3d-paws/3D-PAWS-Print-Files/Rain Gauge Calibration/calibration parts.3mf

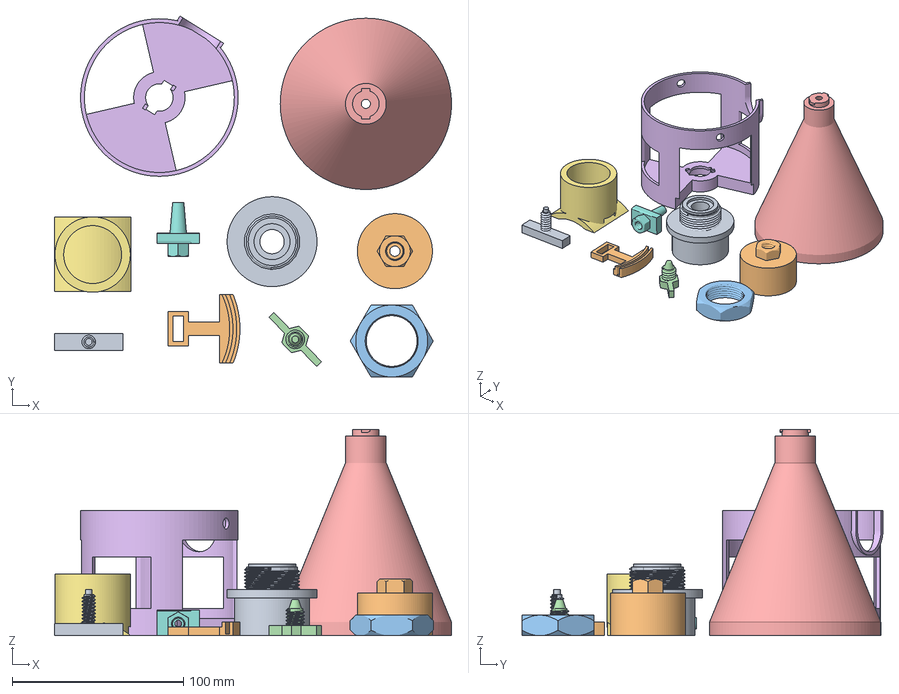
[picture p15: CAD file, 2026-02-17]
Rain Gauge Calibration/calibration parts.3mf
231.8 x 210.8 x 120.5 mm
CF valve top.stl
CF valve bottom for dip bolt2.stl
box to pipe adaptor nut2.stl
drip bolt.stl
funnel small.stl
inspection cover.stl
universal clamp for 1 in pipe.stl
pumped drip controller2.stl
pumped drip controller piston.stl
pumped drip controller mount.stl
