3d-paws/3D-PAWS-Print-Files/Rain Gauge/Funnel/vertical screen.stl

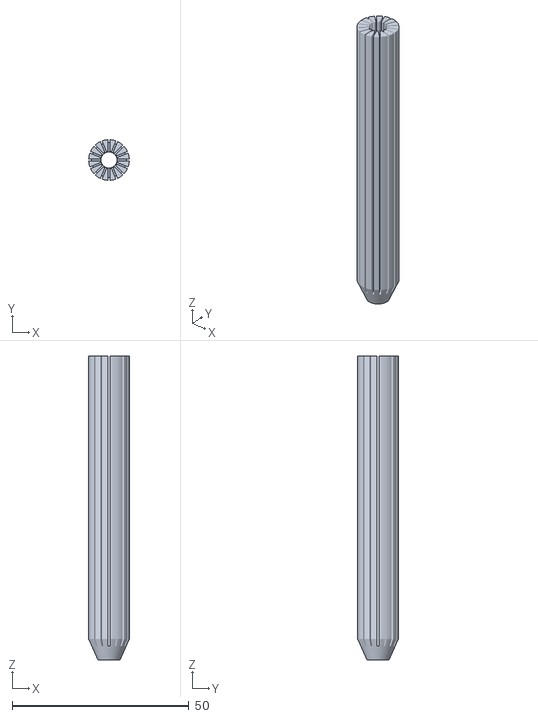
[picture p16: CAD file, 2025-01-10]
Rain Gauge/Funnel/vertical screen.stl
11.5 x 11.5 x 85.9
