3d-paws/3D-PAWS-Print-Files/Snow Gauge/Snow_Gauge.3mf

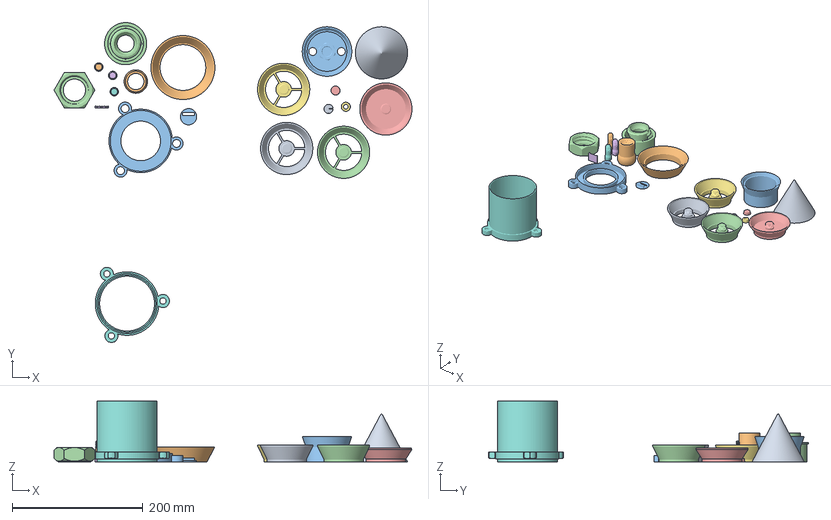
[picture p17: CAD file, 2026-01-30]
Snow Gauge/Snow_Gauge.3mf
548.4 x 490.0 x 93.0 mm
snow cone cover.stl
swivel.stl
Snow gauge rad shield base.stl
swivel lock nut.stl
top leaf snow.stl
shield bolt.stl x 3
open leaf snow.stl x 3
swivel cover.stl
blanking plug.stl
glue tray.stl
temp sensor plug.stl
SG sensor cover.stl
TPH harness plug.stl
collar no tee.stl
upper clamping ring for 2 in pipe.stl
2 in internal swivel threads.stl
