3d-paws/3D-PAWS-Print-Files/Soil Moisture and Temperature/2 cable inlet plug.stl

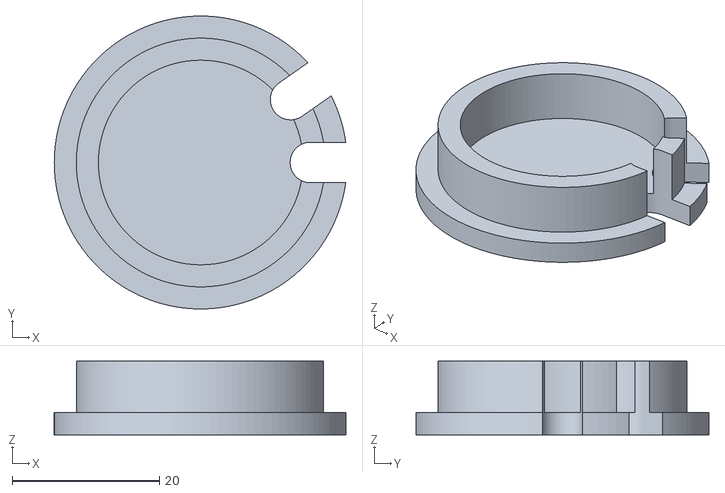
[picture p18: CAD file, 2026-01-30]
Soil Moisture and Temperature/2 cable inlet plug.stl
39.6 x 39.8 x 10.0
