3d-paws/3D-PAWS-Print-Files/Soil Moisture and Temperature/Installation Tool/top pivot.stl

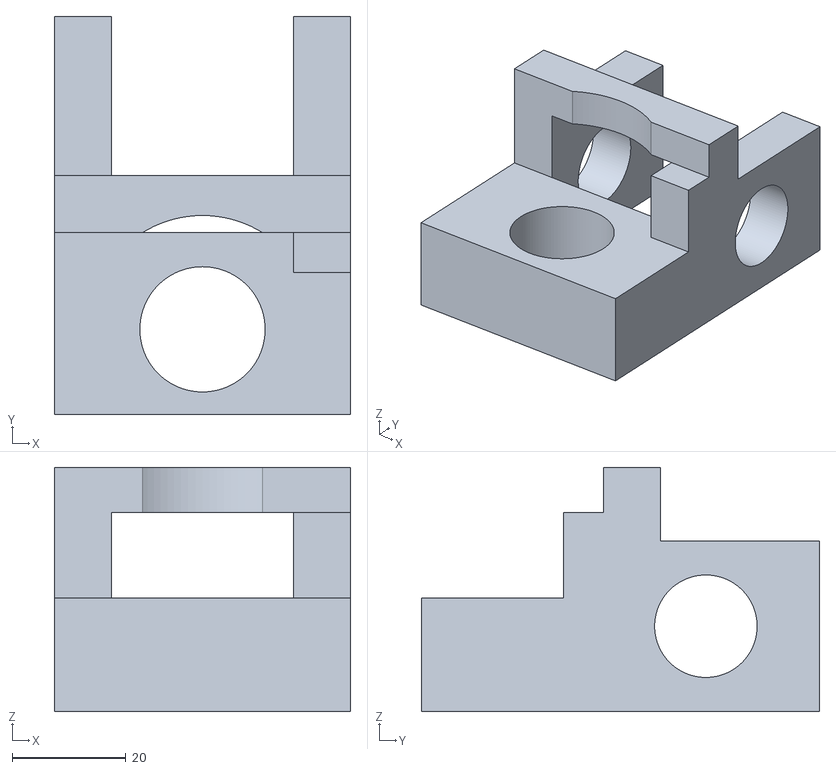
[picture p19: CAD file, 2025-10-24]
Soil Moisture and Temperature/Installation Tool/top pivot.stl
52.0 x 70.0 x 42.9
