3d-paws/3D-PAWS-Print-Files/Solar Power/voltaic solar.3mf

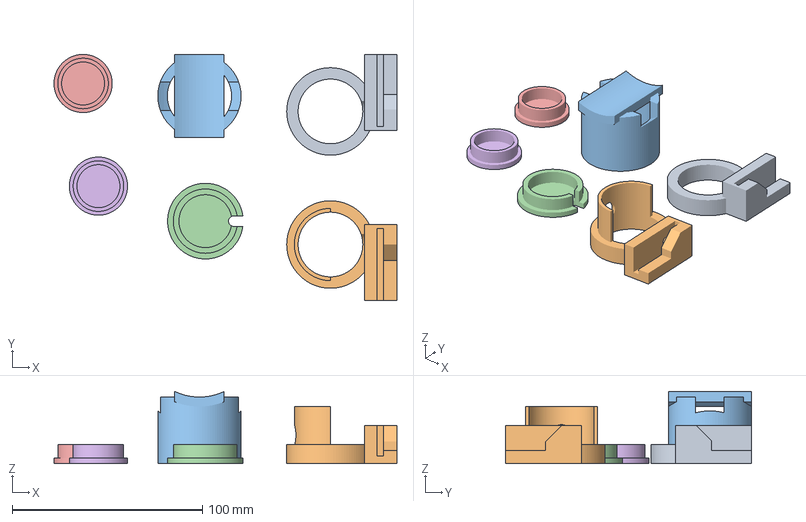
[picture p20: CAD file, 2026-03-06]
Solar Power/voltaic solar.3mf
180.4 x 129.5 x 38.0 mm
efte voltaic clamp.stl
efte voltaic clamp LH.stl
universal clamp for 1 in pipe2.stl
cable inlet plug.stl
1 in end cap.stl x 2
