3d-paws/3D-PAWS-Print-Files/Stream Gauge/2 in internal swivel threads.stl

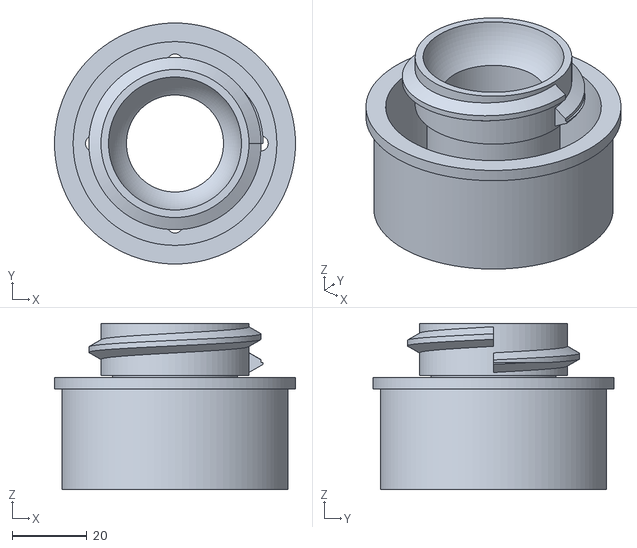
[picture p21: CAD file, 2026-01-30]
Stream Gauge/2 in internal swivel threads.stl
64.6 x 64.6 x 44.5
