3d-paws/3D-PAWS-Print-Files/Tools/wind vane magnet press tool.stl

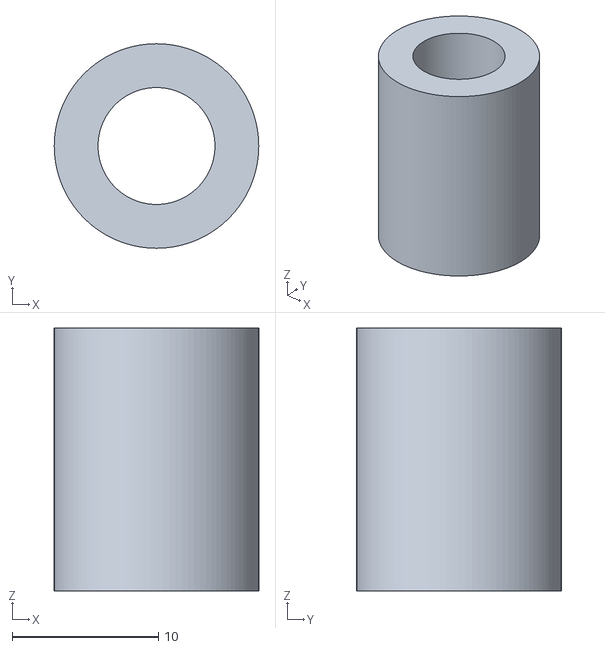
[picture p22: CAD file, 2026-03-10]
Tools/wind vane magnet press tool.stl
14.0 x 14.0 x 18.0
