3d-paws/3D-PAWS-Print-Files/Variable Diameter Pipe/32mm/1 in pipe plug.stl

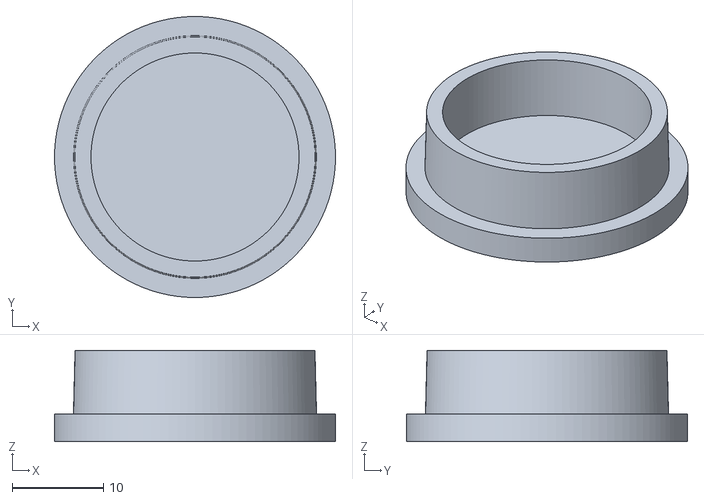
[picture p23: CAD file, 2026-02-09]
Variable Diameter Pipe/32mm/1 in pipe plug.stl
30.8 x 30.8 x 10.0
