3d-paws/3D-PAWS-Print-Files/Variable Diameter Pipe/scad files/box to pipe adaptor nut2.stl

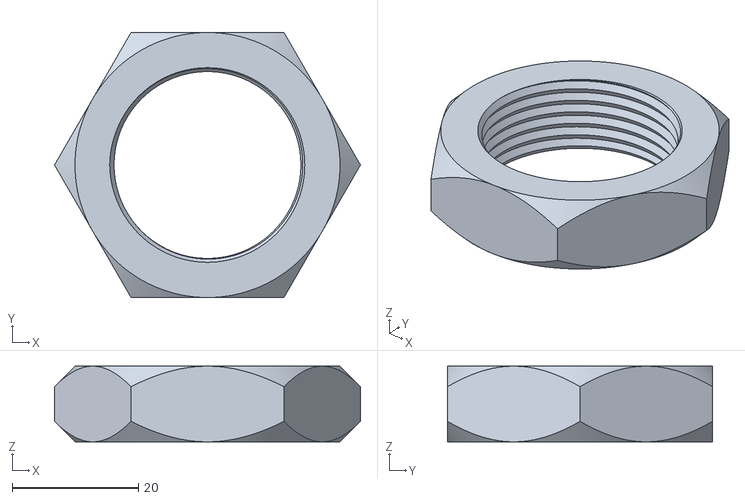
[picture p24: CAD file, 2026-02-09]
Variable Diameter Pipe/scad files/box to pipe adaptor nut2.stl
48.5 x 42.0 x 12.0
