3d-paws/3D-PAWS-Print-Files/Air Quality/air quality 2nd leaf.stl

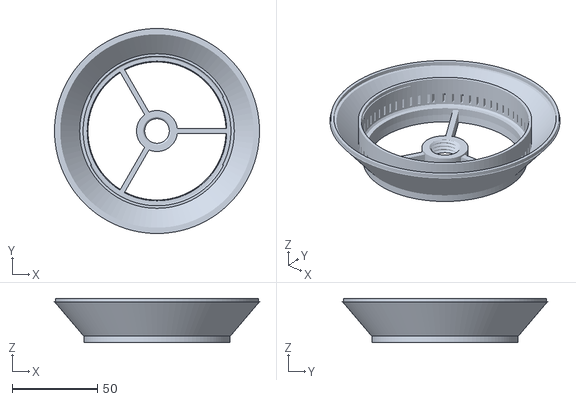
[picture p25: CAD file, 2026-02-04]
Air Quality/air quality 2nd leaf.stl
120.0 x 120.0 x 25.9
