3d-paws/3D-PAWS-Print-Files/Anemometer/bearing holder.stl

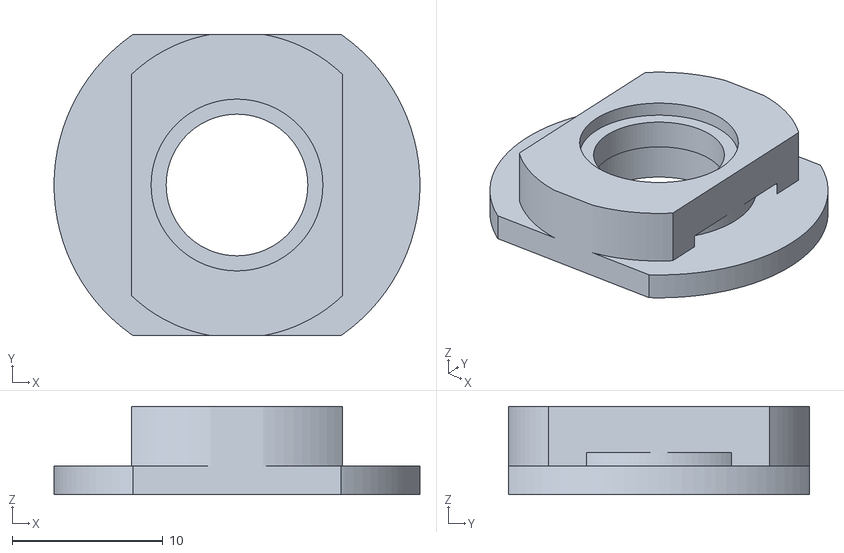
[picture p26: CAD file, 2026-03-05]
Anemometer/bearing holder.stl
24.3 x 20.0 x 5.85
