3d-paws/3D-PAWS-Print-Files/Black Globe/3in black globe.3mf

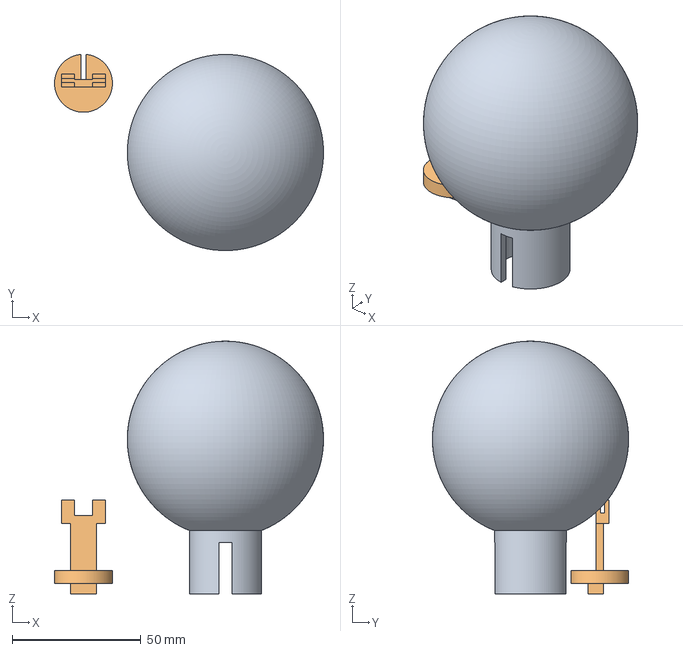
[picture p27: CAD file, 2025-04-08]
Black Globe/3in black globe.3mf
104.4 x 76.2 x 98.1 mm
black globe.stl
globe sensor holder.stl
