3d-paws/3D-PAWS-Print-Files/Data Logger/antenna clip MKR.stl

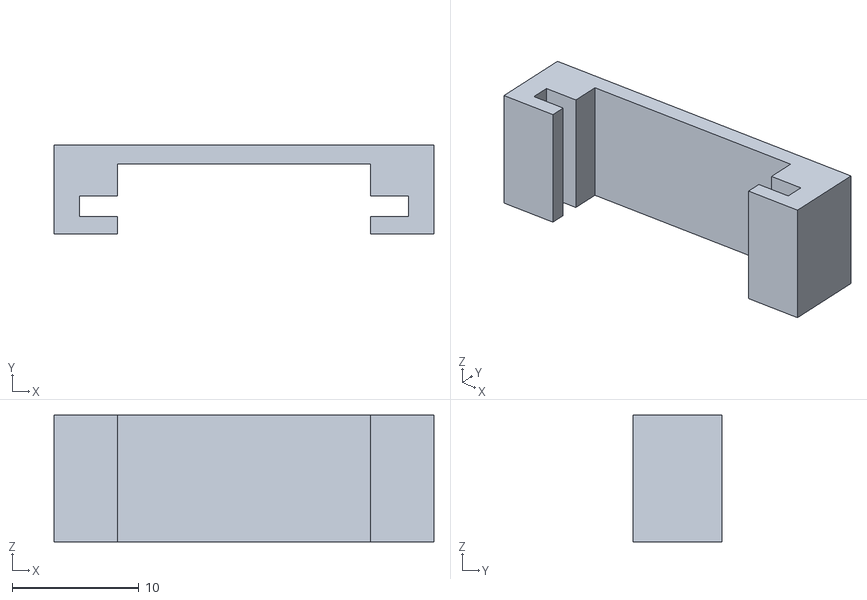
[picture p28: CAD file, 2026-03-26]
Data Logger/antenna clip MKR.stl
30.0 x 7.00 x 10.0
