3d-paws/3D-PAWS-Print-Files/Light Sensor/body.stl

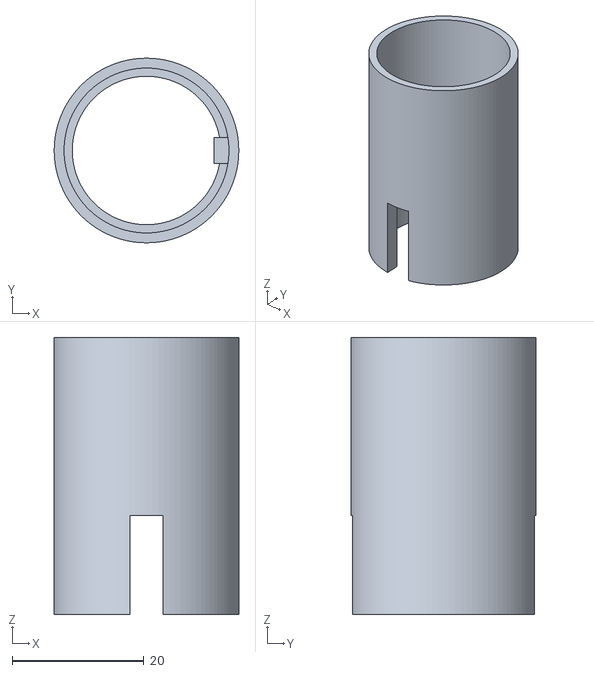
[picture p29: CAD file, 2025-01-09]
Light Sensor/body.stl
28.0 x 28.0 x 42.0
