3d-paws/3D-PAWS-Print-Files/Radiation Shield and Wiring/RS Assembly/top leaf no shaft.stl

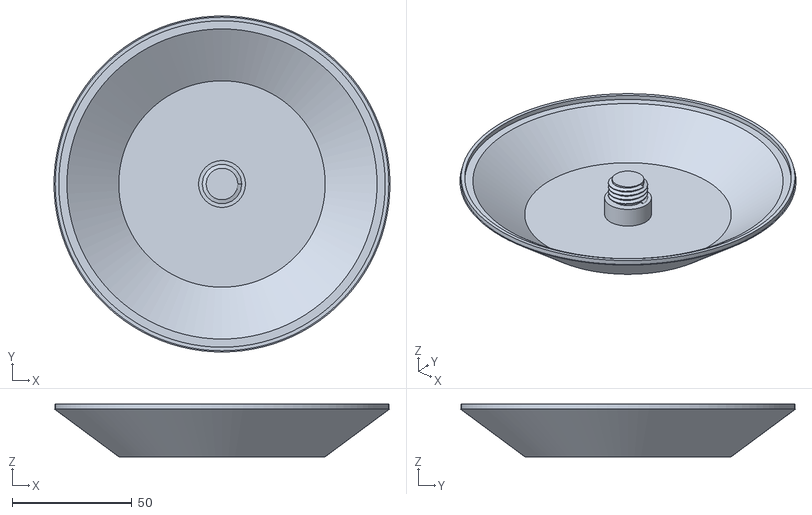
[picture p30: CAD file, 2025-01-09]
Radiation Shield and Wiring/RS Assembly/top leaf no shaft.stl
140.0 x 140.0 x 21.9
