3d-paws/3D-PAWS-Print-Files/Radiation Shield and Wiring/Wiring/mount.stl

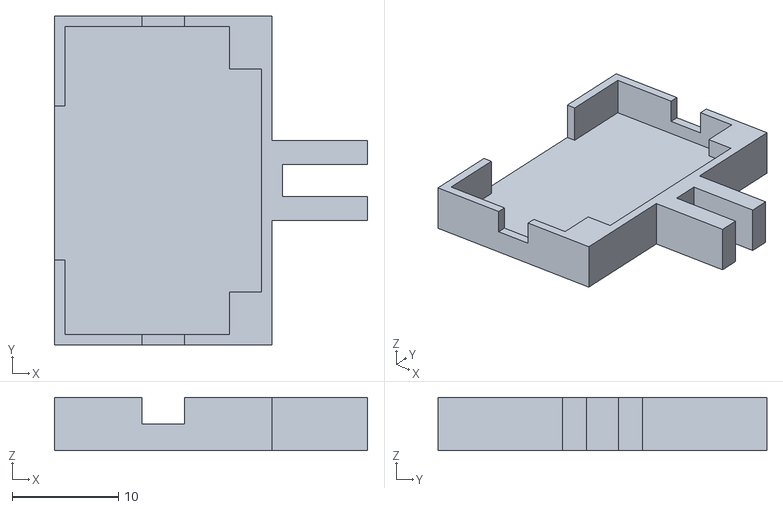
[picture p31: CAD file, 2025-01-09]
Radiation Shield and Wiring/Wiring/mount.stl
29.5 x 31.0 x 5.00
