3d-paws/3D-PAWS-Print-Files/Rain Gauge Calibration/pumped drip controller mount.stl

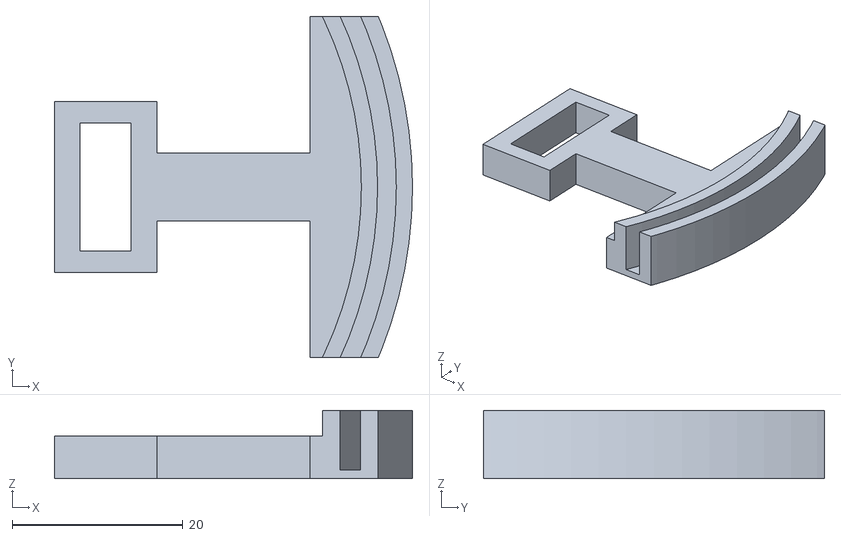
[picture p32: CAD file, 2025-01-10]
Rain Gauge Calibration/pumped drip controller mount.stl
42.0 x 40.0 x 8.00
