3d-paws/3D-PAWS-Print-Files/Rain Gauge/counter balance.stl

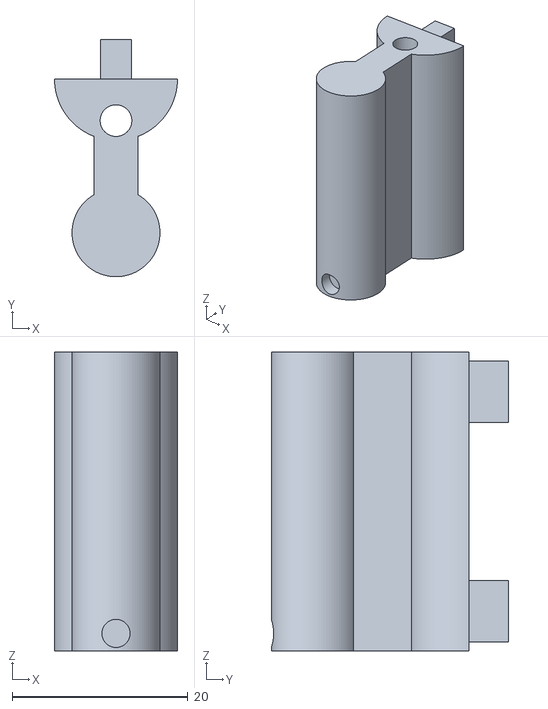
[picture p33: CAD file, 2026-02-02]
Rain Gauge/counter balance.stl
14.0 x 27.0 x 34.0
