3d-paws/3D-PAWS-Print-Files/Rain Gauge/Funnel/vertical screen support.stl

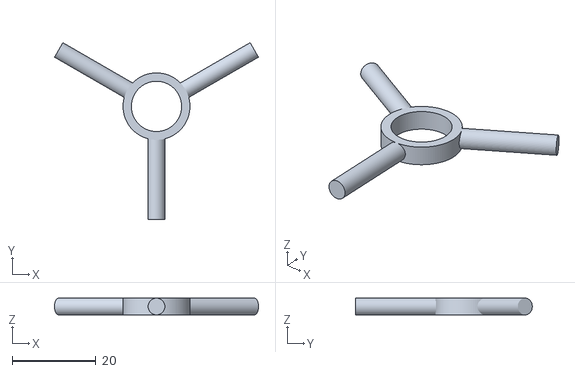
[picture p34: CAD file, 2025-01-10]
Rain Gauge/Funnel/vertical screen support.stl
48.8 x 42.2 x 4.00
