3d-paws/3D-PAWS-Print-Files/Snow Gauge/collar no tee.stl

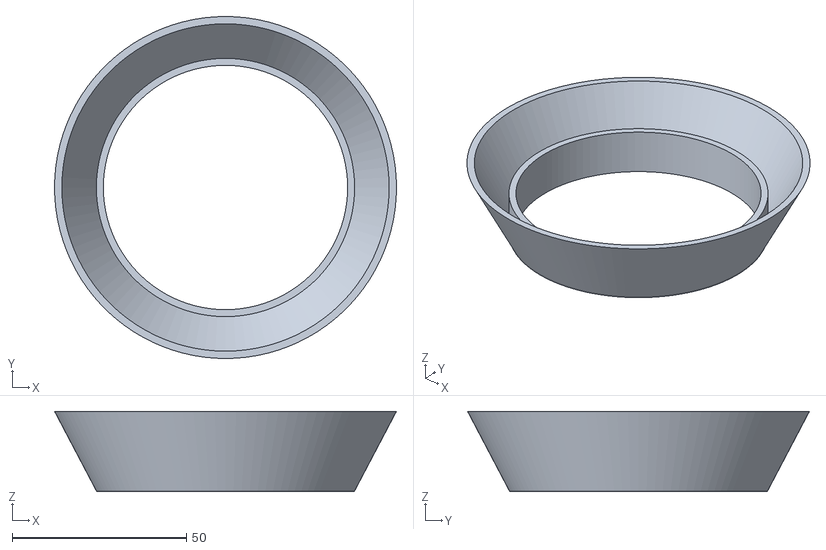
[picture p35: CAD file, 2026-01-30]
Snow Gauge/collar no tee.stl
98.0 x 98.0 x 23.0
