3d-paws/3D-PAWS-Print-Files/Stream Gauge/stream or storm gauge.3mf

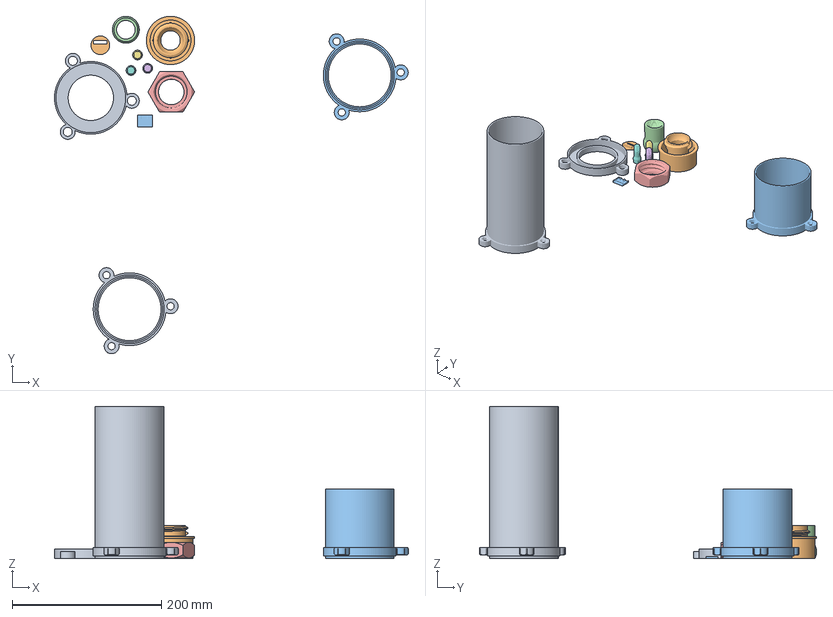
[picture p37: CAD file, 2026-01-30]
Stream Gauge/stream or storm gauge.3mf
473.6 x 451.3 x 204.0 mm
storm surge sensor shield.stl
2 in internal swivel threads.stl
sensor shield.stl
swivel.stl
swivel lock nut.stl
shield bolt.stl x 3
upper clamping ring for 2 in pipe.stl
swivel cover.stl
glue tray.stl
