3d-paws/3D-PAWS-Print-Files/Tools/stand off 2in post with strap.stl

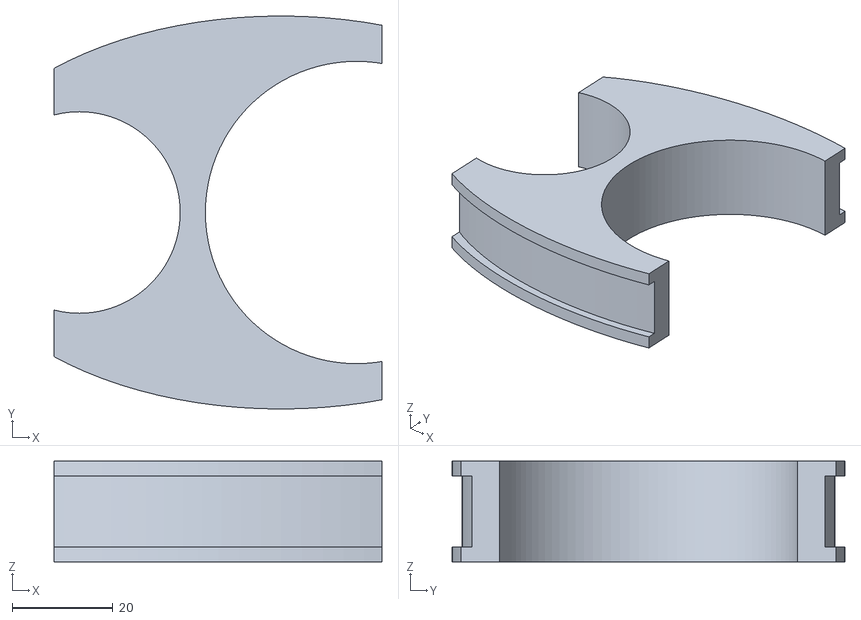
[picture p38: CAD file, 2026-03-05]
Tools/stand off 2in post with strap.stl
65.0 x 78.0 x 20.0
