3d-paws/3D-PAWS-Print-Files/Air Quality/AQ screen ring.stl

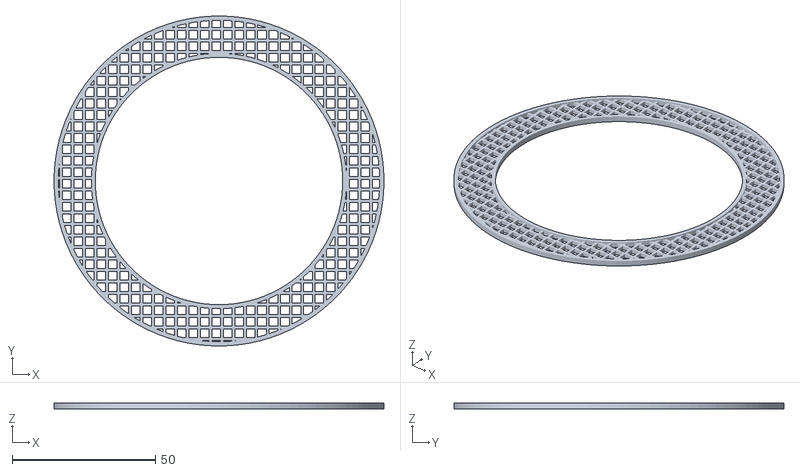
[picture p39: CAD file, 2026-02-04]
Air Quality/AQ screen ring.stl
115.0 x 115.0 x 2.00
