3d-paws/3D-PAWS-Print-Files/Anemometer/threaded shaft WS.stl

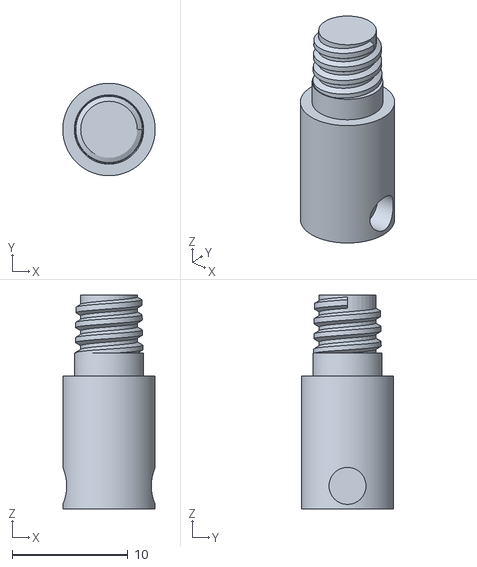
[picture p40: CAD file, 2025-12-08]
Anemometer/threaded shaft WS.stl
8.00 x 8.00 x 18.5
