3d-paws/3D-PAWS-Print-Files/Black Globe/6in globe sensor holder.stl

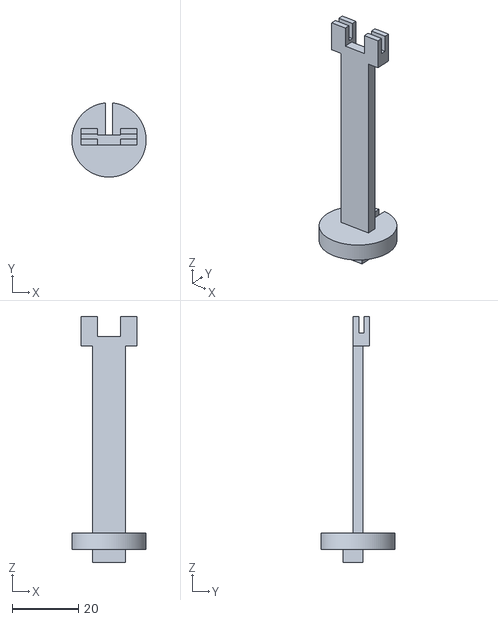
[picture p41: CAD file, 2025-04-08]
Black Globe/6in globe sensor holder.stl
22.5 x 22.5 x 74.4
