3d-paws/3D-PAWS-Print-Files/Data Logger/rack for box and battery RH.stl

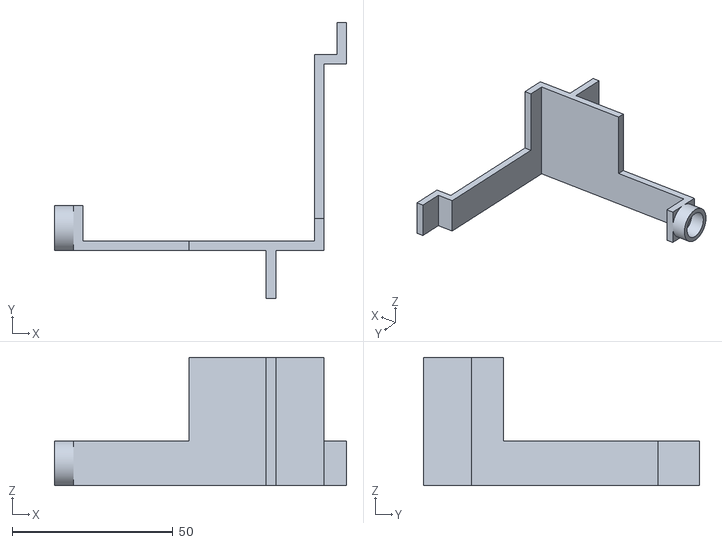
[picture p42: CAD file, 2026-03-02]
Data Logger/rack for box and battery RH.stl
90.9 x 86.0 x 40.0
