3d-paws/3D-PAWS-Print-Files/Light Sensor/cover.stl

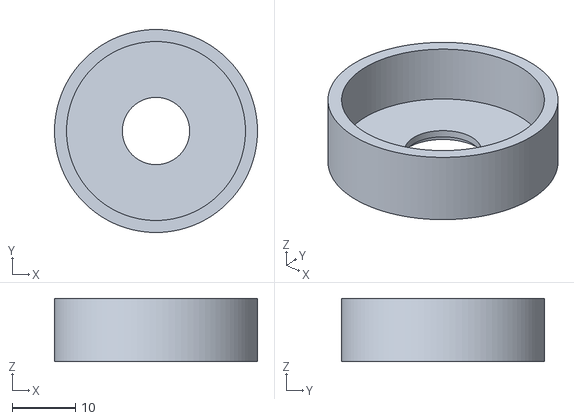
[picture p43: CAD file, 2025-01-09]
Light Sensor/cover.stl
32.0 x 32.0 x 10.0
