3d-paws/3D-PAWS-Print-Files/Radiation Shield and Wiring/RS Assembly/locking threads.stl

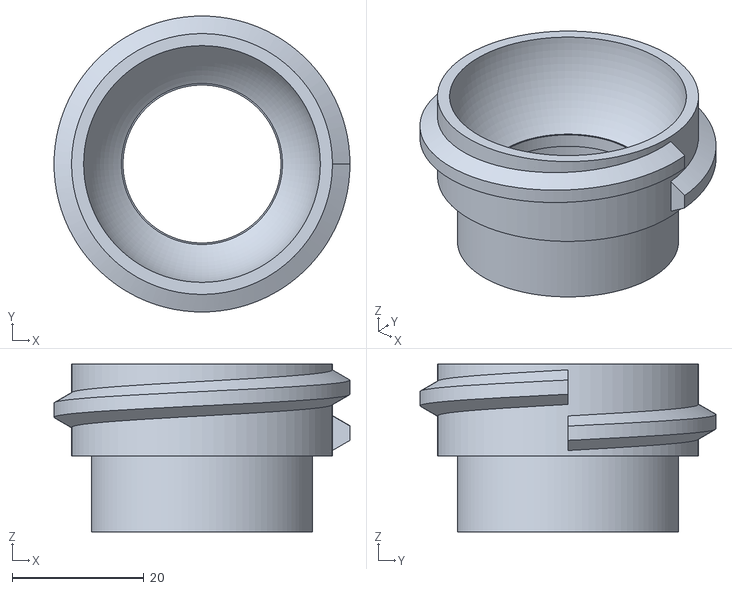
[picture p44: CAD file, 2025-01-09]
Radiation Shield and Wiring/RS Assembly/locking threads.stl
45.0 x 45.0 x 25.5
