3d-paws/3D-PAWS-Print-Files/Radiation Shield and Wiring/Wiring/mcp breather.stl

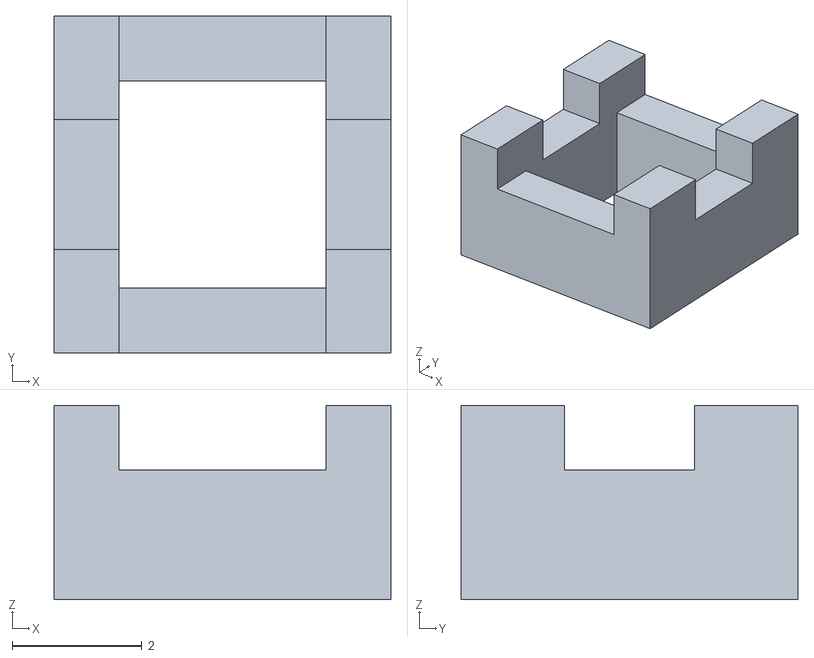
[picture p45: CAD file, 2025-01-09]
Radiation Shield and Wiring/Wiring/mcp breather.stl
5.20 x 5.20 x 3.00
