3d-paws/3D-PAWS-Print-Files/Rain Gauge Calibration/large reservoir flow control.3mf

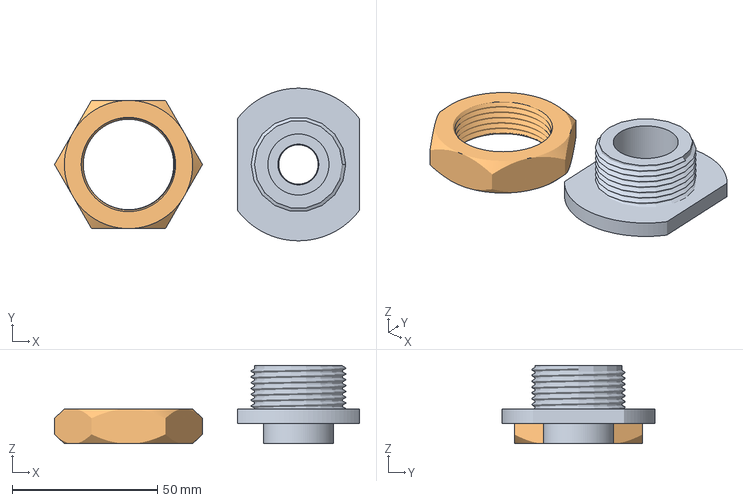
[picture p46: CAD file, 2025-01-10]
Rain Gauge Calibration/large reservoir flow control.3mf
104.9 x 52.5 x 27.0 mm
flow control for large reservoir.stl
flow control securing nut.stl
