3d-paws/3D-PAWS-Print-Files/Rain Gauge/6.5 stop.stl

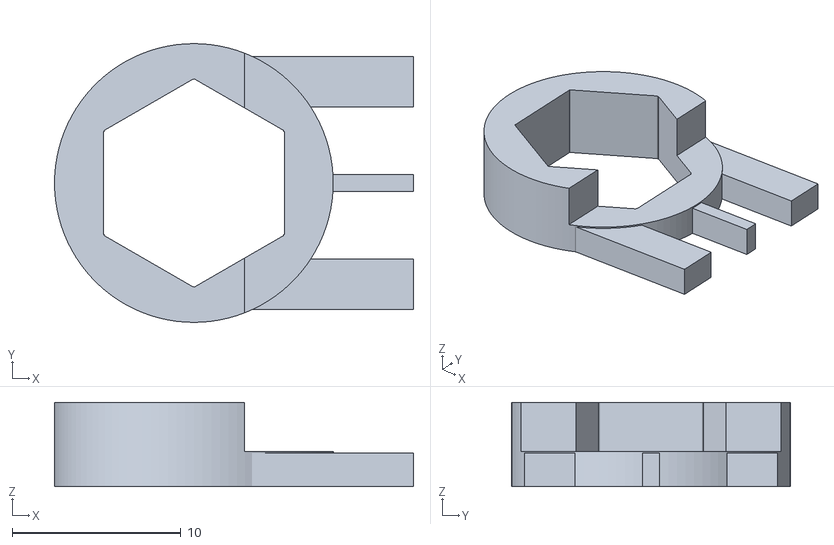
[picture p47: CAD file, 2026-01-30]
Rain Gauge/6.5 stop.stl
21.2 x 16.5 x 5.00
