3d-paws/3D-PAWS-Print-Files/Rain Gauge/Funnel/fixed funnel.stl

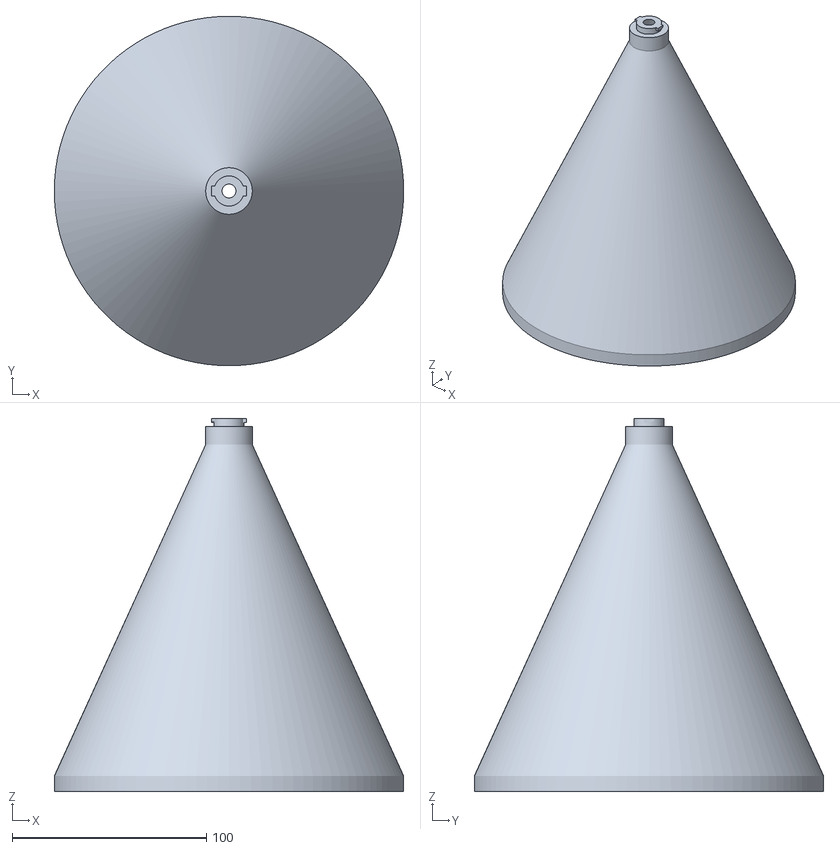
[picture p48: CAD file, 2025-01-10]
Rain Gauge/Funnel/fixed funnel.stl
180.0 x 180.0 x 192.2
