3d-paws/3D-PAWS-Print-Files/Soil Moisture and Temperature/Installation Tool/pipe end pivot.stl

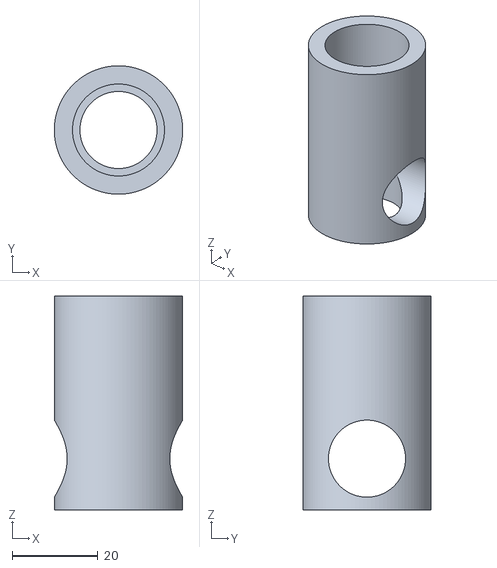
[picture p50: CAD file, 2025-10-24]
Soil Moisture and Temperature/Installation Tool/pipe end pivot.stl
30.0 x 30.0 x 50.0
