3d-paws/3D-PAWS-Print-Files/Solar Power/efte voltaic clamp LH.stl

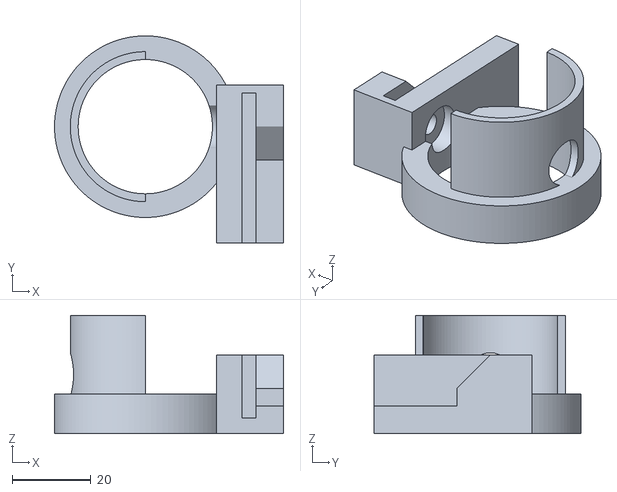
[picture p51: CAD file, 2025-01-10]
Solar Power/efte voltaic clamp LH.stl
58.0 x 52.5 x 30.0
