3d-paws/3D-PAWS-Print-Files/Station Assembly/box adapter female.stl

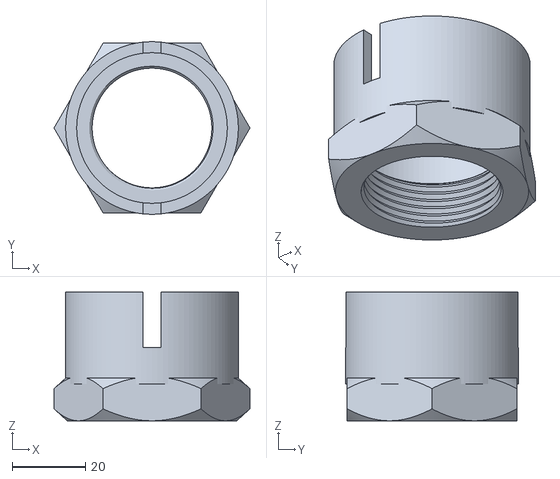
[picture p52: CAD file, 2025-01-10]
Station Assembly/box adapter female.stl
53.3 x 47.0 x 35.0
