3d-paws/3D-PAWS-Print-Files/Stream Gauge/storm surge sensor shield.stl

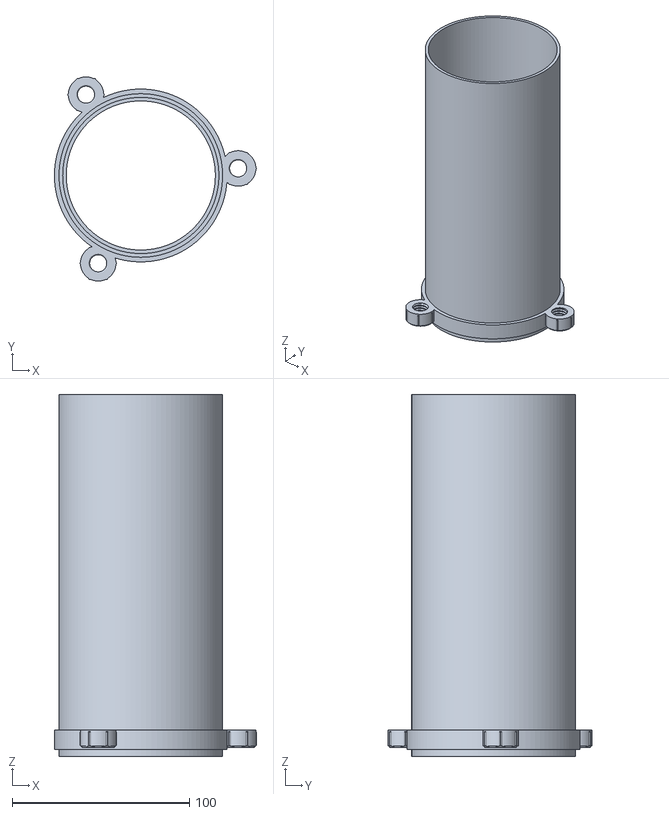
[picture p53: CAD file, 2025-01-15]
Stream Gauge/storm surge sensor shield.stl
114.0 x 115.0 x 204.0
