3d-paws/3D-PAWS-Print-Files/Variable Diameter Pipe/32mm/RG lower cover clamp.stl

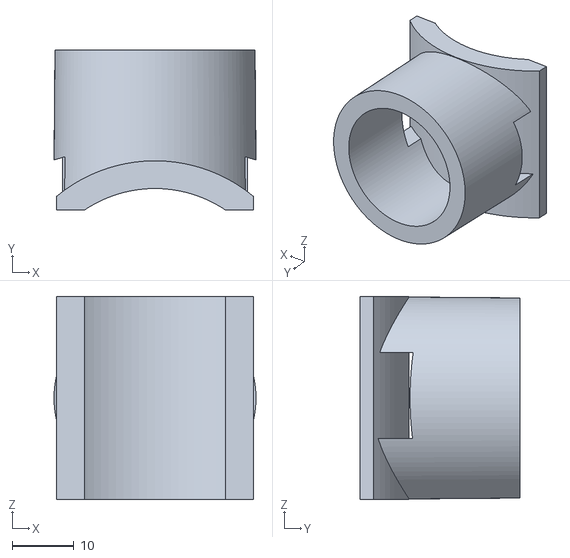
[picture p55: CAD file, 2026-02-09]
Variable Diameter Pipe/32mm/RG lower cover clamp.stl
32.8 x 26.0 x 33.0
