3d-paws/3D-PAWS-Print-Files/Wind Vane/threaded shaft WD.stl

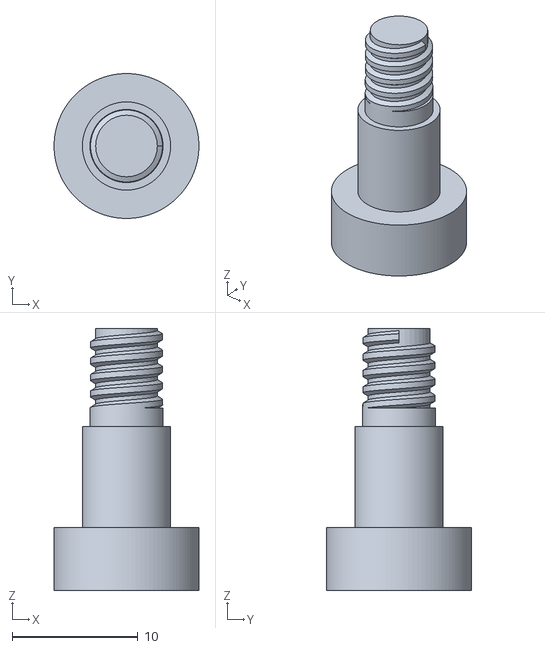
[picture p56: CAD file, 2026-02-25]
Wind Vane/threaded shaft WD.stl
11.5 x 11.5 x 20.8
