3d-paws/3D-PAWS-Print-Files/Anemometer/threaded hub.stl

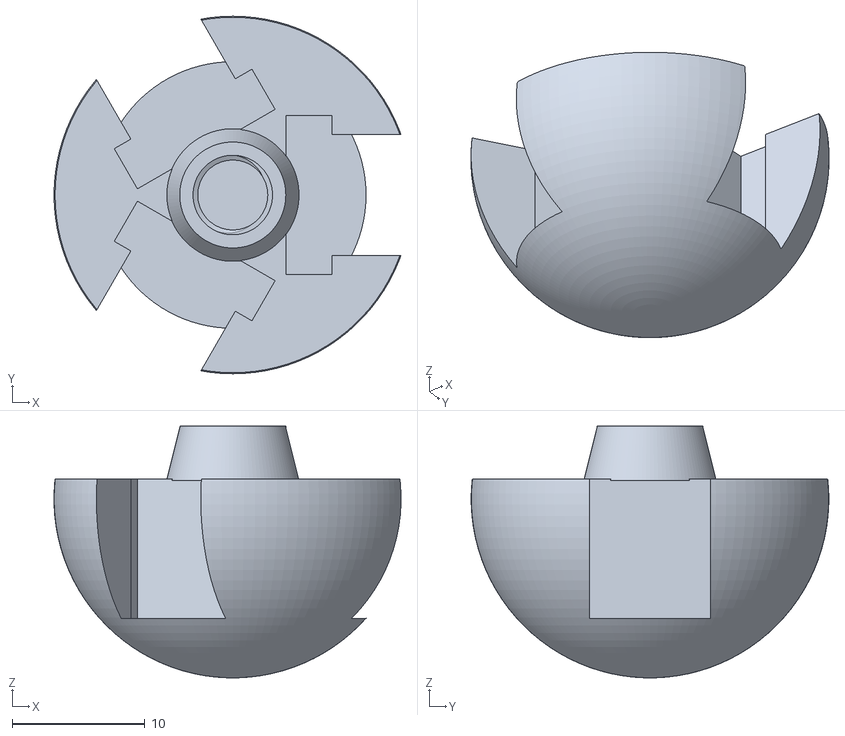
[picture p58: CAD file, 2025-12-08]
Anemometer/threaded hub.stl
26.2 x 27.0 x 19.0
