3d-paws/3D-PAWS-Print-Files/Black Globe/3in globe sensor holder.stl

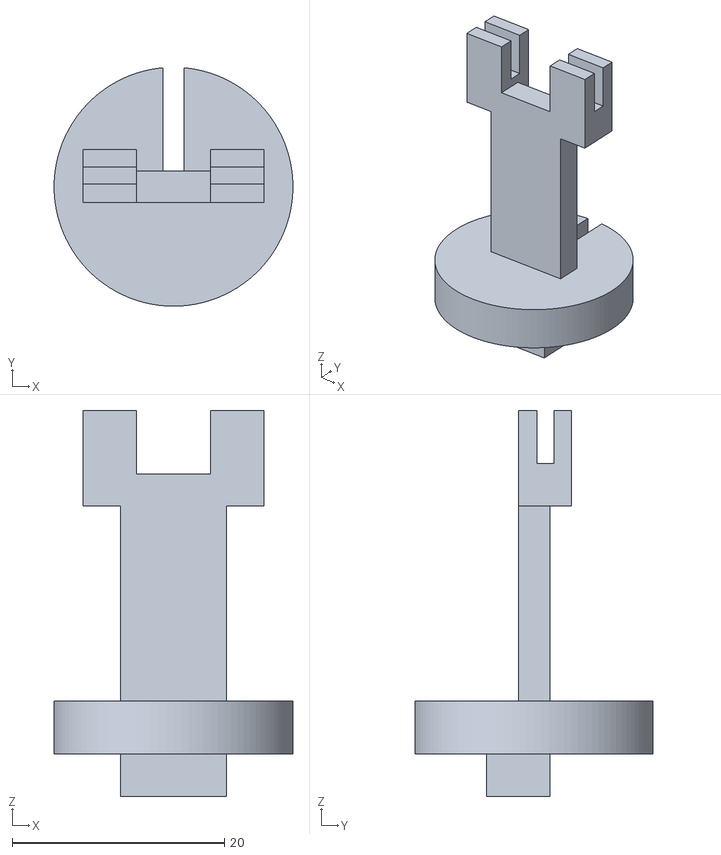
[picture p59: CAD file, 2025-03-27]
Black Globe/3in globe sensor holder.stl
22.5 x 22.5 x 36.3
