3d-paws/3D-PAWS-Print-Files/Radiation Shield and Wiring/RS Assembly/screen ring max.stl

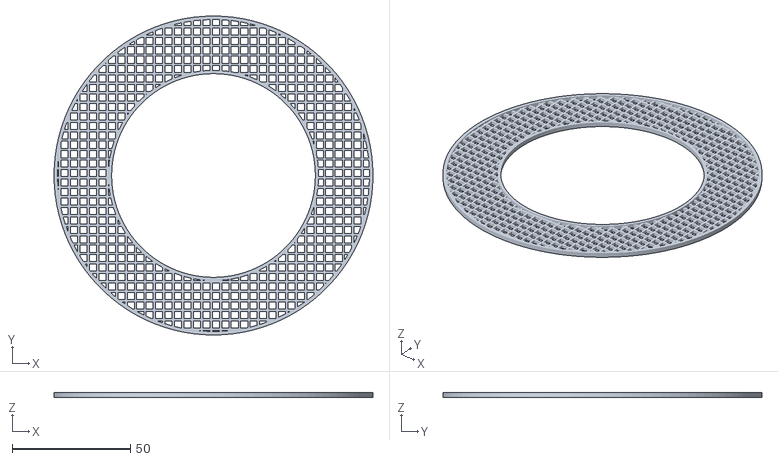
[picture p60: CAD file, 2025-01-09]
Radiation Shield and Wiring/RS Assembly/screen ring max.stl
135.0 x 135.0 x 2.00
