3d-paws/3D-PAWS-Print-Files/Radiation Shield and Wiring/Wiring/sensor holders.3mf

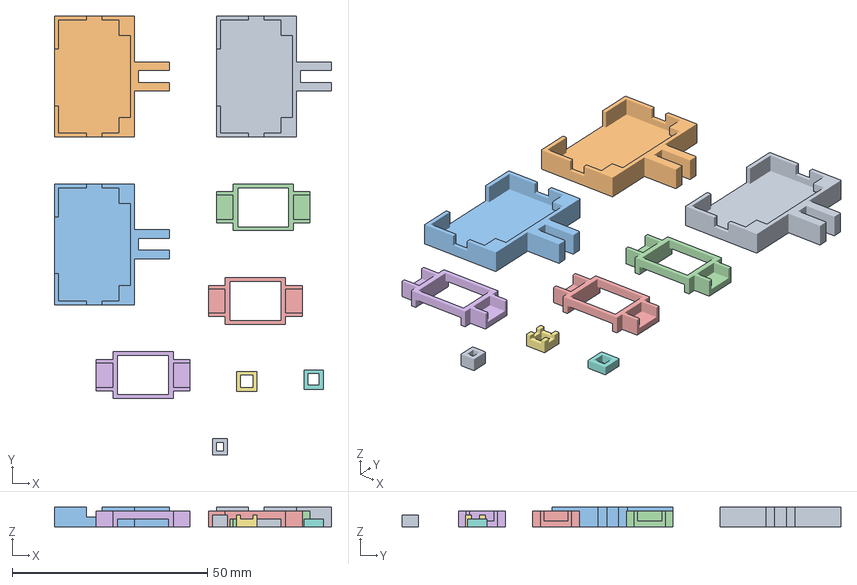
[picture p61: CAD file, 2025-01-09]
Radiation Shield and Wiring/Wiring/sensor holders.3mf
71.0 x 112.4 x 5.00 mm
new mount.stl x 3
glue cover.stl x 3
mcp breather.stl
sht breather.stl
bmp breather.stl
