3d-paws/3D-PAWS-Print-Files/Rain Gauge Calibration/pumped drip controller piston.stl

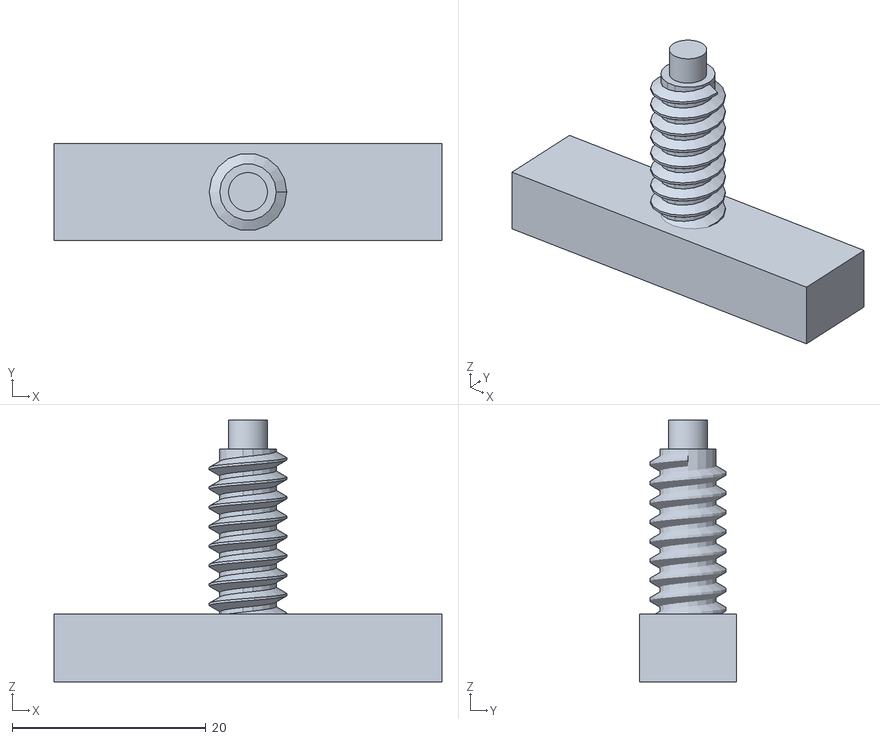
[picture p62: CAD file, 2025-01-10]
Rain Gauge Calibration/pumped drip controller piston.stl
40.0 x 10.0 x 27.0
