3d-paws/3D-PAWS-Print-Files/Rain Gauge/base.stl

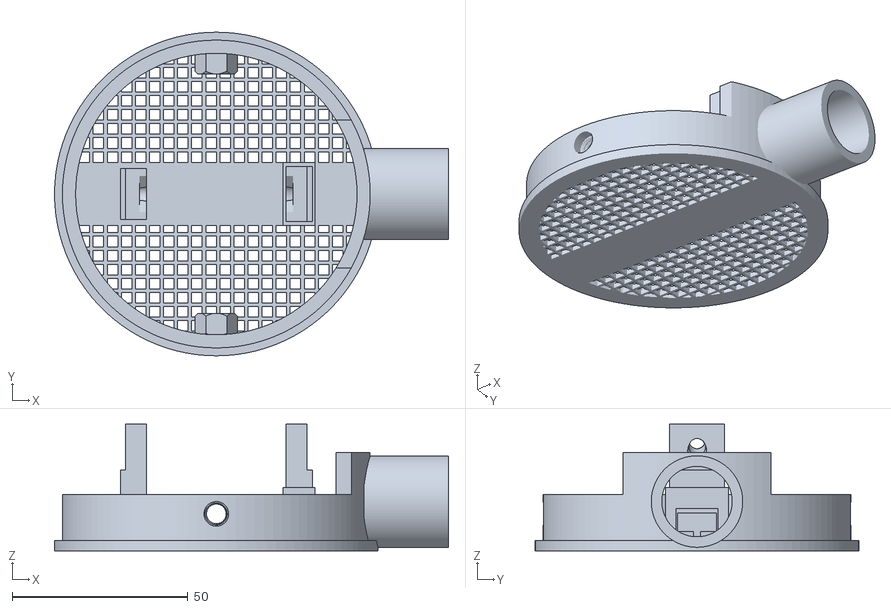
[picture p63: CAD file, 2026-01-30]
Rain Gauge/base.stl
112.0 x 92.0 x 36.0
