3d-paws/3D-PAWS-Print-Files/Rain Gauge/Funnel/vertical screen cap.stl

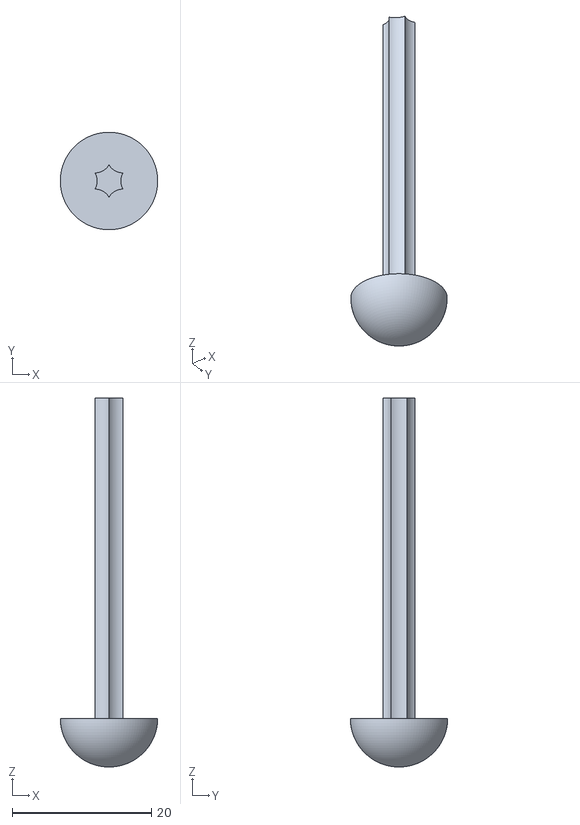
[picture p64: CAD file, 2025-01-10]
Rain Gauge/Funnel/vertical screen cap.stl
14.0 x 14.0 x 53.0
