3d-paws/3D-PAWS-Print-Files/Snow Gauge/upper clamping ring for 2 in pipe.stl

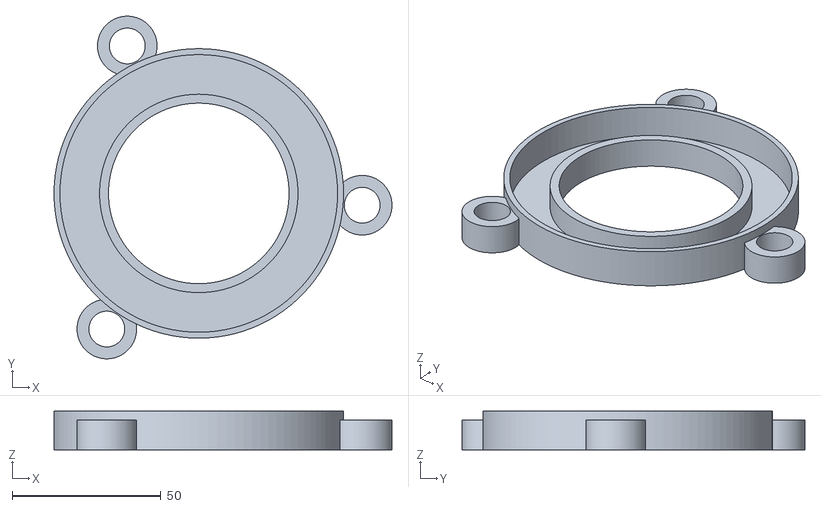
[picture p65: CAD file, 2026-01-30]
Snow Gauge/upper clamping ring for 2 in pipe.stl
113.5 x 115.0 x 13.0
