3d-paws/3D-PAWS-Print-Files/Soil Moisture and Temperature/grove mux case and lid.stl

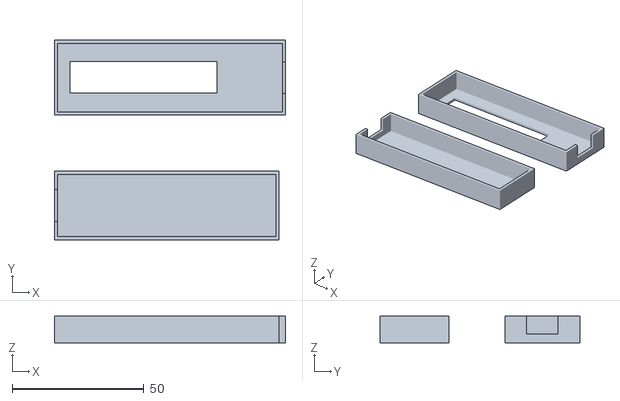
[picture p66: CAD file, 2025-10-24]
Soil Moisture and Temperature/grove mux case and lid.stl
87.8 x 75.9 x 10.2
