3d-paws/3D-PAWS-Print-Files/Soil Moisture and Temperature/Installation Tool/PM WCS 3 insert seat4.stl

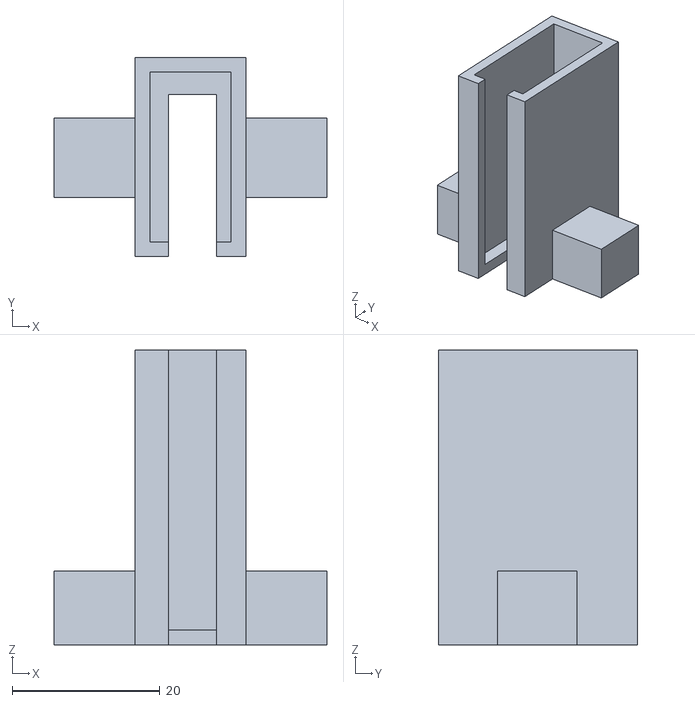
[picture p67: CAD file, 2025-10-24]
Soil Moisture and Temperature/Installation Tool/PM WCS 3 insert seat4.stl
37.0 x 27.0 x 40.0
