3d-paws/3D-PAWS-Print-Files/Solar Power/efte voltaic clamp.stl

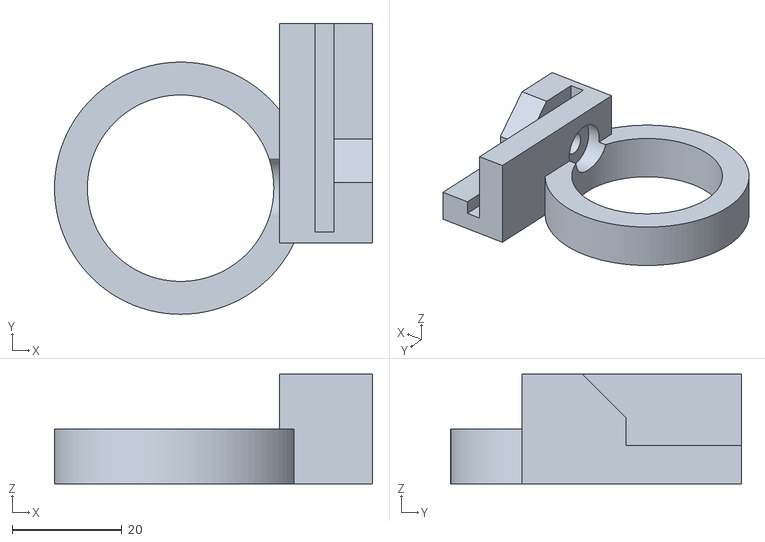
[picture p68: CAD file, 2025-01-10]
Solar Power/efte voltaic clamp.stl
58.0 x 53.0 x 20.0
