3d-paws/3D-PAWS-Print-Files/Station Assembly/small M5 connector lid.stl

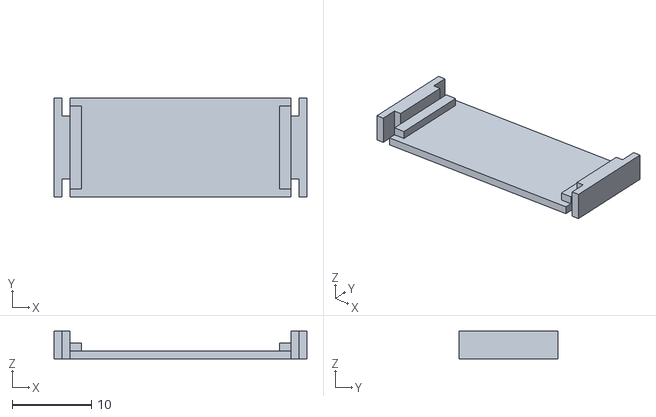
[picture p69: CAD file, 2025-01-10]
Station Assembly/small M5 connector lid.stl
32.0 x 12.5 x 3.50
