3d-paws/3D-PAWS-Print-Files/Stream Gauge/glue tray.stl

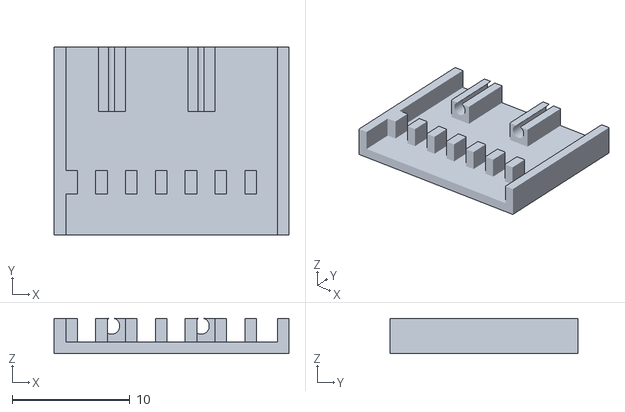
[picture p70: CAD file, 2025-01-10]
Stream Gauge/glue tray.stl
20.0 x 16.0 x 3.00
