3d-paws/3D-PAWS-Print-Files/Variable Diameter Pipe/32mm/end cap for 1in fitting.stl

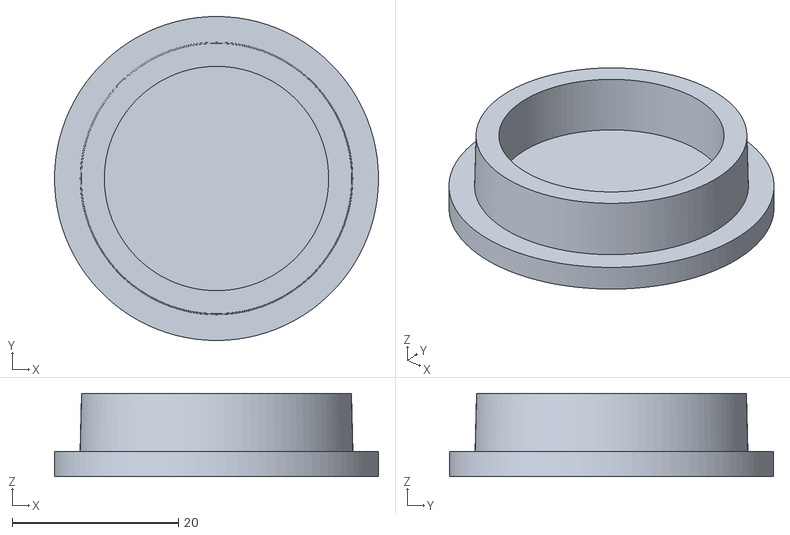
[picture p72: CAD file, 2026-02-09]
Variable Diameter Pipe/32mm/end cap for 1in fitting.stl
39.0 x 39.0 x 10.0
