3d-paws/3D-PAWS-Print-Files/Wind Vane/base.stl

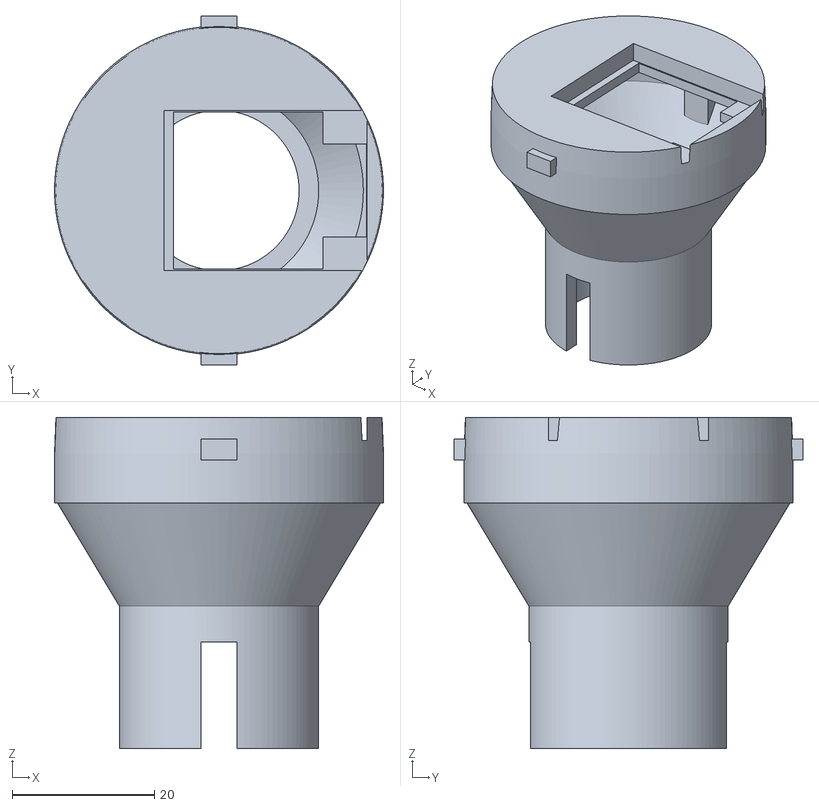
[picture p73: CAD file, 2026-02-17]
Wind Vane/base.stl
46.2 x 49.0 x 46.5
