3d-paws/3D-PAWS-Print-Files/Air Quality/air quality open leaf.stl

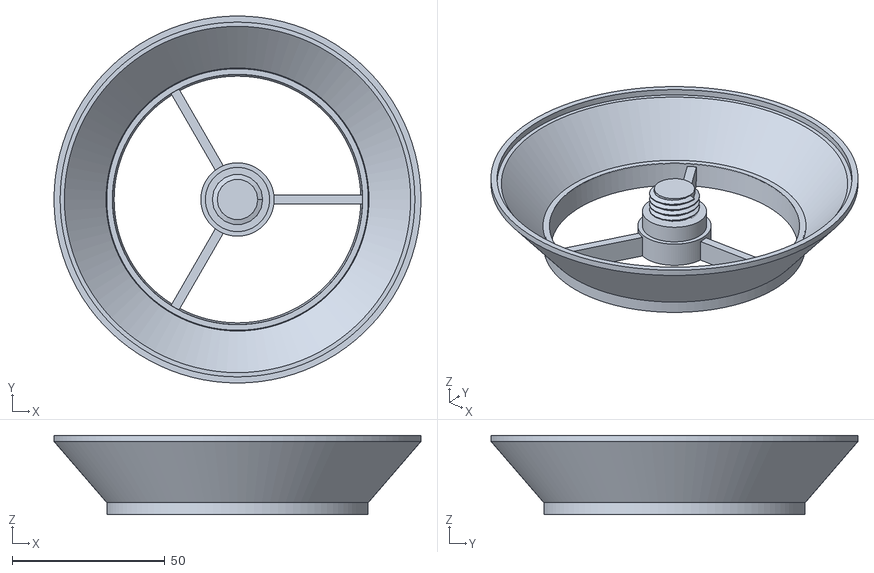
[picture p74: CAD file, 2026-02-04]
Air Quality/air quality open leaf.stl
120.0 x 120.0 x 25.9
