3d-paws/3D-PAWS-Print-Files/Anemometer/base.stl

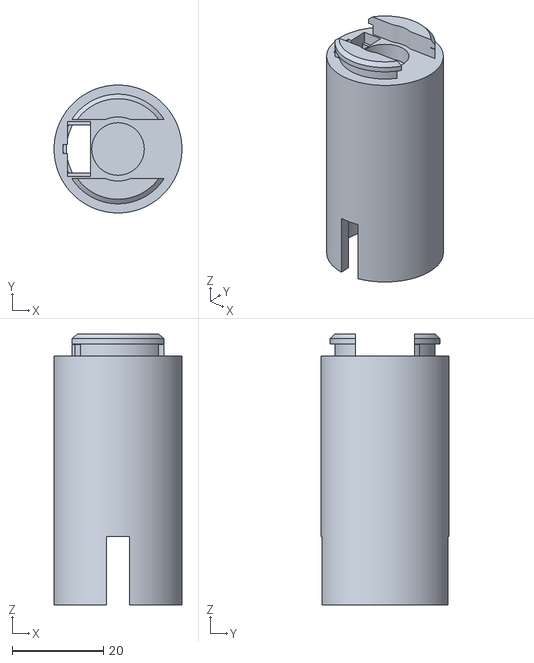
[picture p75: CAD file, 2025-01-09]
Anemometer/base.stl
28.0 x 28.0 x 59.3
