3d-paws/3D-PAWS-Print-Files/Data Logger/data logger box lid rack.3mf

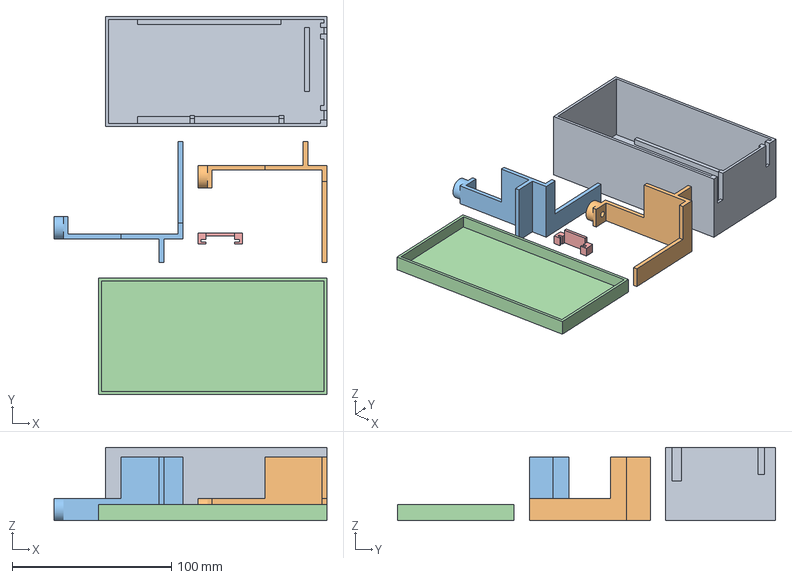
[picture p76: CAD file, 2026-01-30]
Data Logger/data logger box lid rack.3mf
171.3 x 237.2 x 46.0 mm
data logger box with dividers.stl
rack for box and battery LH.stl
rack for box and battery RH.stl
data logger box with dividers lid.stl
antenna clip boron.stl
