3d-paws/3D-PAWS-Print-Files/Light Sensor/sensor holder.stl

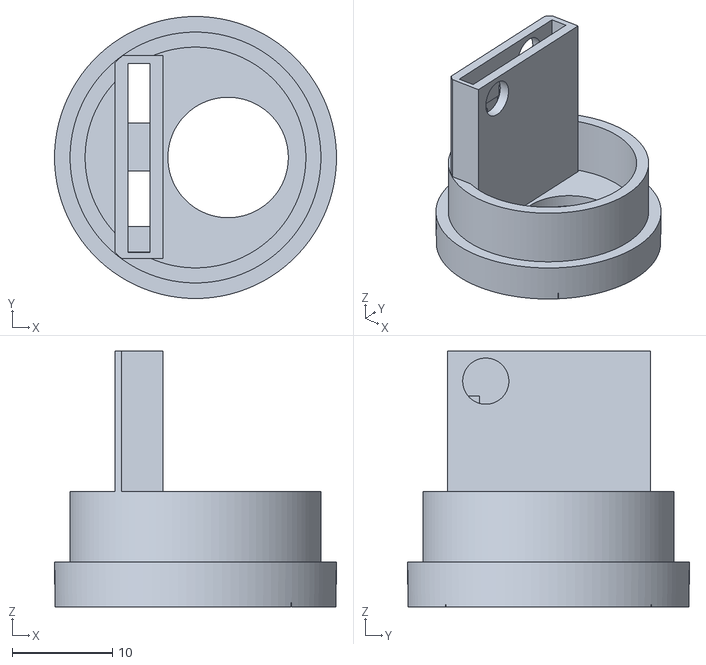
[picture p77: CAD file, 2025-01-09]
Light Sensor/sensor holder.stl
28.1 x 28.1 x 25.5
