3d-paws/3D-PAWS-Print-Files/Radiation Shield and Wiring/Wiring/bmp breather.stl

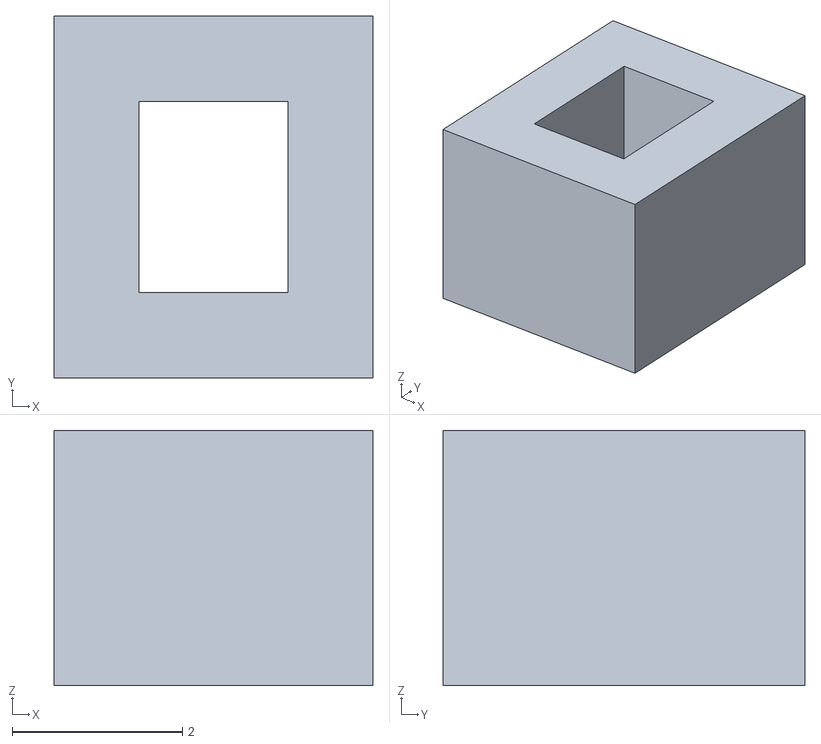
[picture p79: CAD file, 2025-01-09]
Radiation Shield and Wiring/Wiring/bmp breather.stl
3.75 x 4.25 x 3.00
