3d-paws/3D-PAWS-Print-Files/Rain Gauge Calibration/funnel small.stl

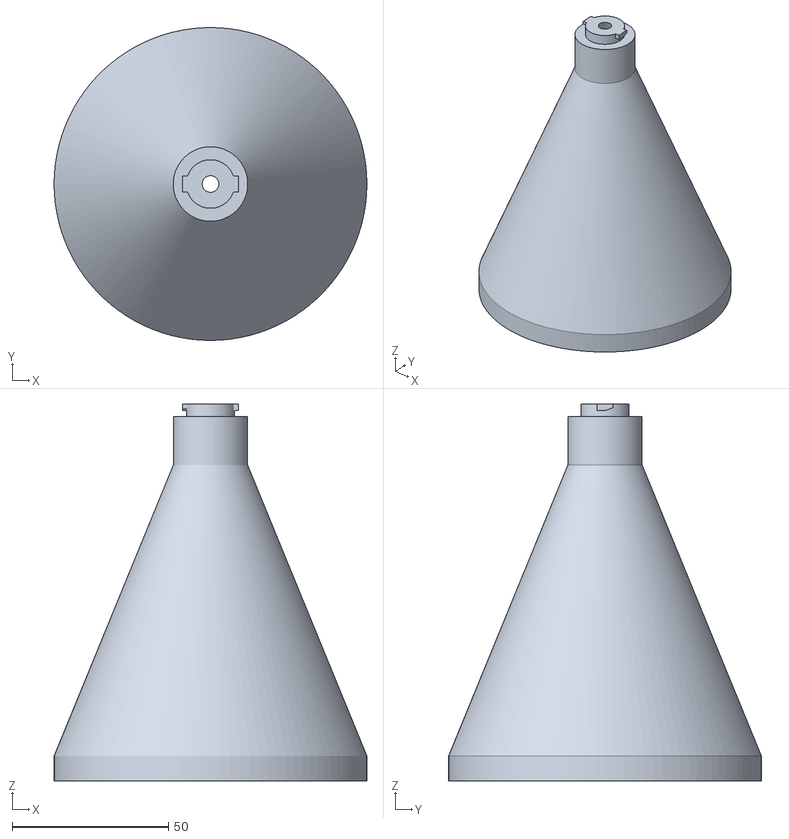
[picture p80: CAD file, 2025-01-10]
Rain Gauge Calibration/funnel small.stl
100.0 x 100.0 x 120.5
