3d-paws/3D-PAWS-Print-Files/Rain Gauge/3D-PAWS cover.stl

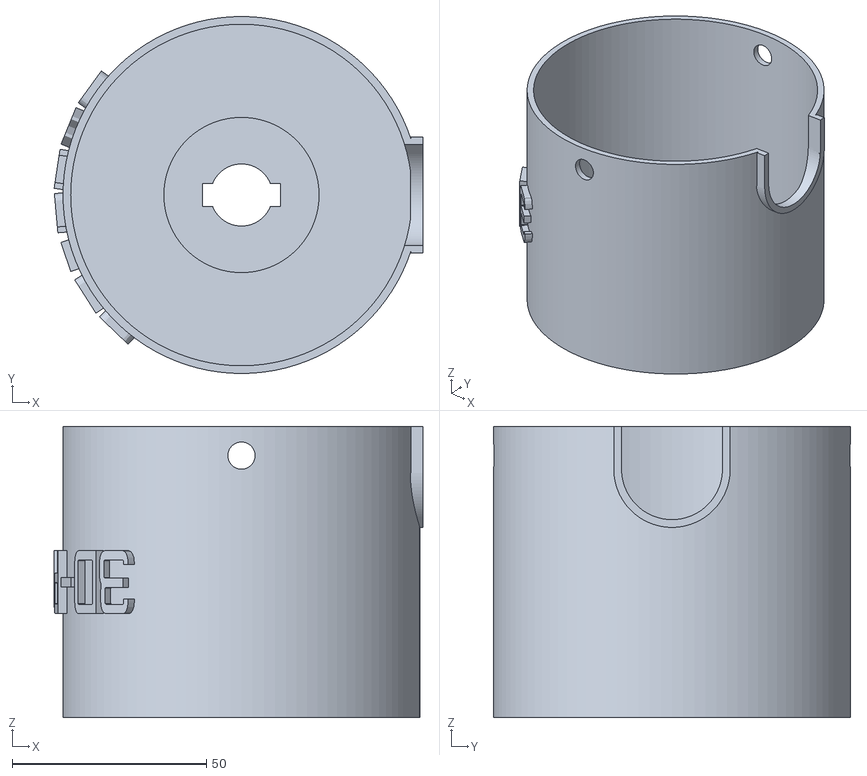
[picture p81: CAD file, 2026-01-30]
Rain Gauge/3D-PAWS cover.stl
95.0 x 92.0 x 75.0
