3d-paws/3D-PAWS-Print-Files/Rain Gauge/Funnel/Horizontal screen.stl

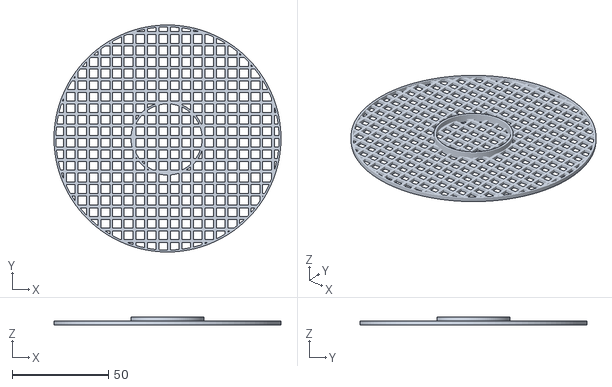
[picture p82: CAD file, 2025-01-10]
Rain Gauge/Funnel/Horizontal screen.stl
118.0 x 118.0 x 4.00
