3d-paws/3D-PAWS-Print-Files/Soil Moisture and Temperature/ltc box and lid.stl

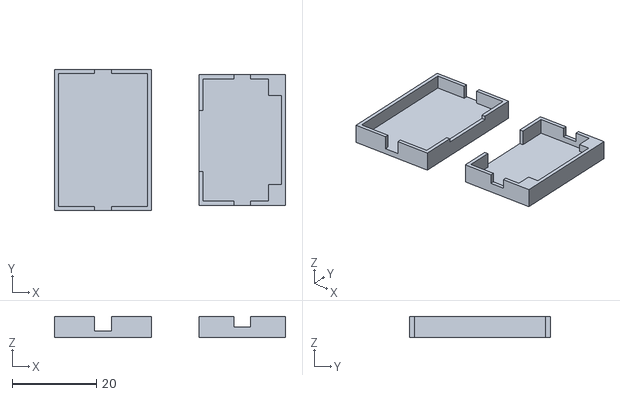
[picture p83: CAD file, 2025-10-24]
Soil Moisture and Temperature/ltc box and lid.stl
54.8 x 33.5 x 5.00
