3d-paws/3D-PAWS-Print-Files/Solar Power/universal clamp for 1 in pipe2.stl

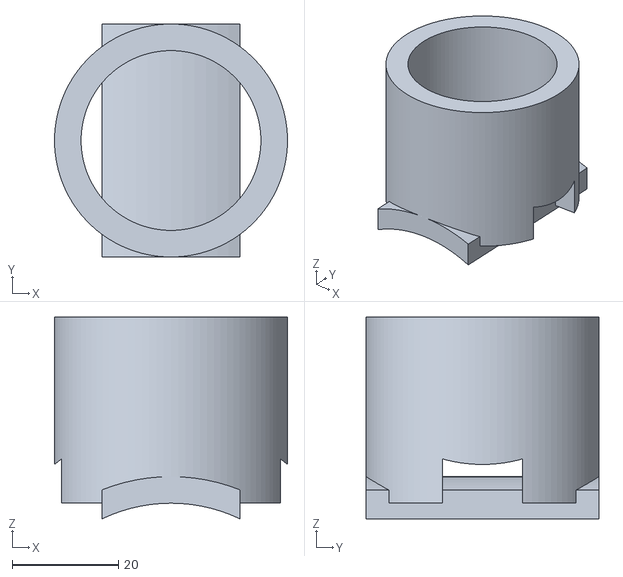
[picture p84: CAD file, 2025-01-10]
Solar Power/universal clamp for 1 in pipe2.stl
43.8 x 43.8 x 38.0
