3d-paws/3D-PAWS-Print-Files/Station Assembly/1in pipe to 3-4 cpvc.stl

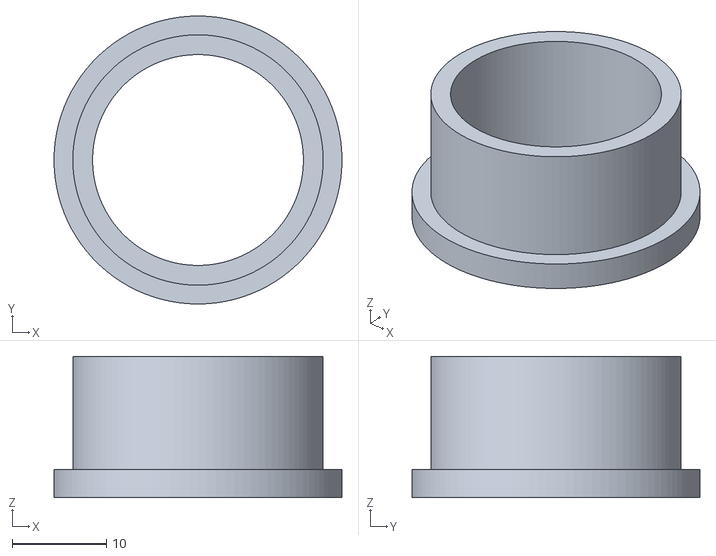
[picture p85: CAD file, 2025-01-10]
Station Assembly/1in pipe to 3-4 cpvc.stl
30.6 x 30.6 x 15.0
