3d-paws/3D-PAWS-Print-Files/Stream Gauge/swivel cover.stl

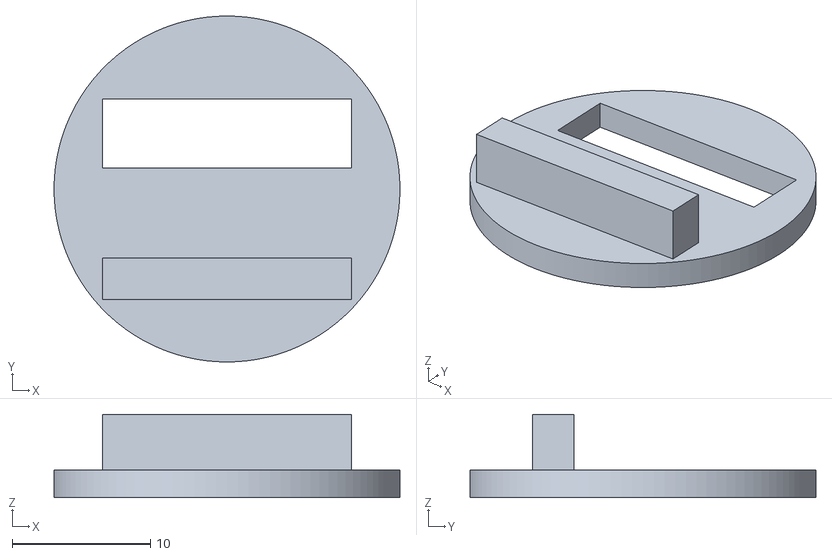
[picture p86: CAD file, 2025-01-10]
Stream Gauge/swivel cover.stl
25.0 x 25.0 x 6.00
