3d-paws/3D-PAWS-Print-Files/Tools/stand off 17_20_Tt_F.stl

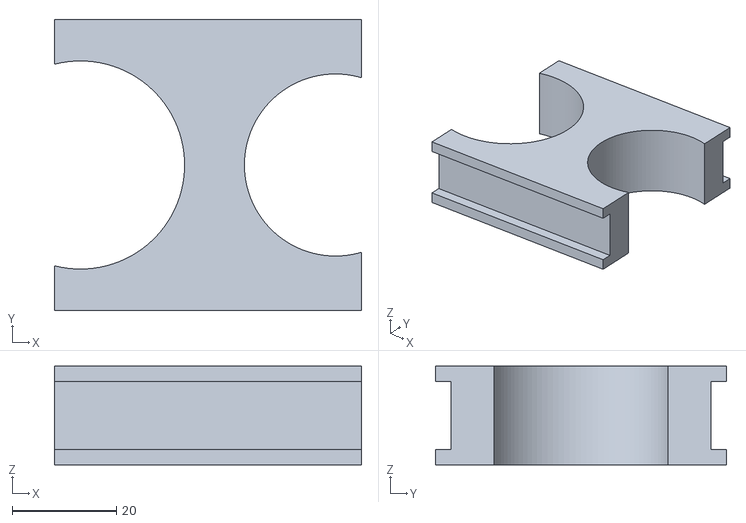
[picture p87: CAD file, 2026-02-27]
Tools/stand off 17_20_Tt_F.stl
59.0 x 56.0 x 19.0
