3d-paws/3D-PAWS-Print-Files/Wind Vane/glue cover.stl

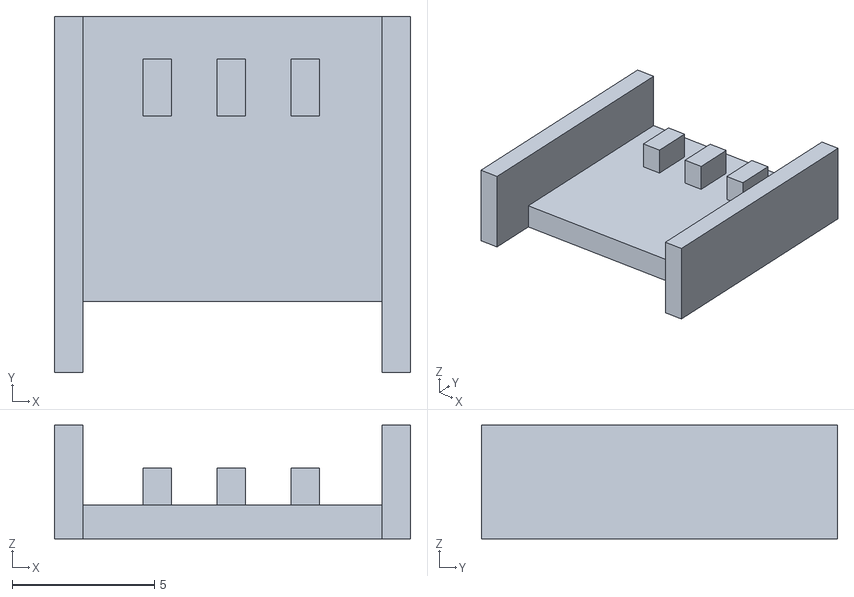
[picture p88: CAD file, 2026-01-30]
Wind Vane/glue cover.stl
12.5 x 12.5 x 4.00
