3d-paws/3D-PAWS-Print-Files/Air Quality/air quality sensor cover.stl

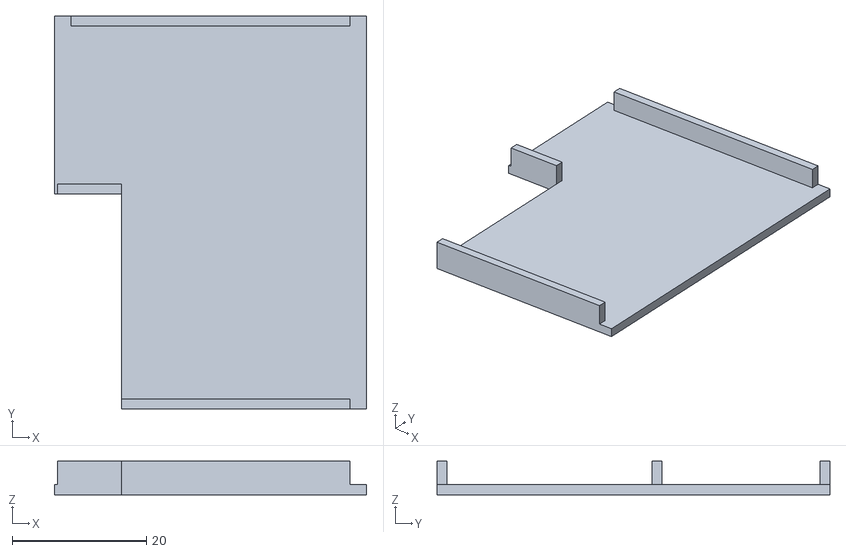
[picture p89: CAD file, 2026-02-04]
Air Quality/air quality sensor cover.stl
46.5 x 58.5 x 5.00
