3d-paws/3D-PAWS-Print-Files/Anemometer/skirt.stl

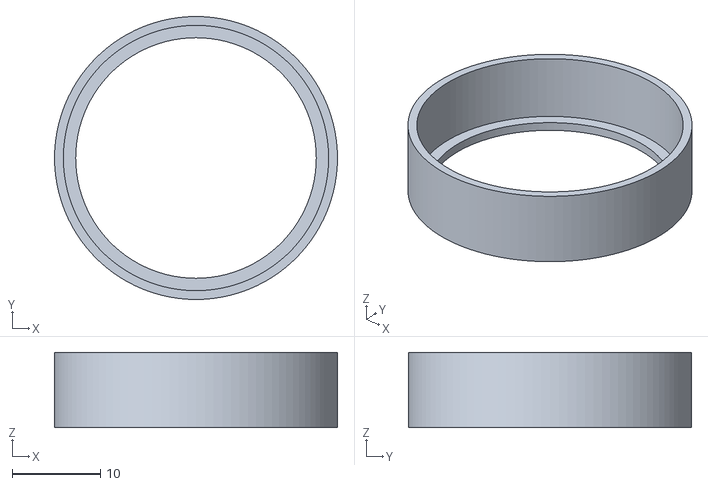
[picture p90: CAD file, 2025-01-09]
Anemometer/skirt.stl
32.0 x 32.0 x 8.50
