3d-paws/3D-PAWS-Print-Files/Data Logger/data logger box with dividers lid.stl

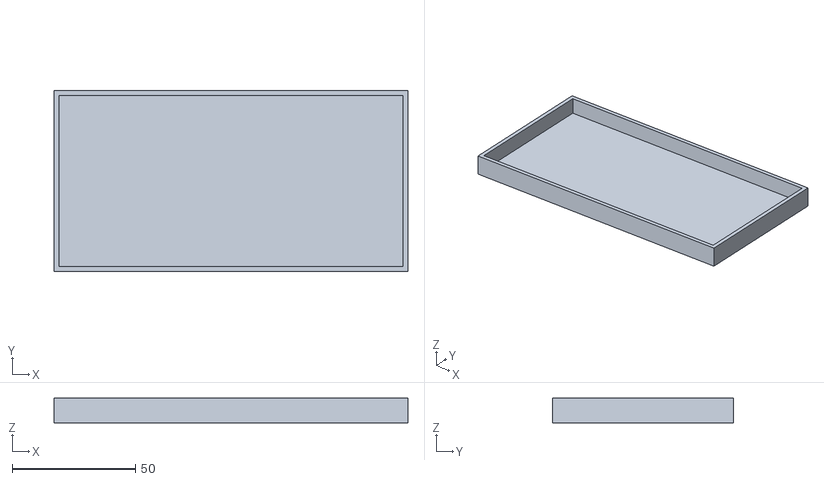
[picture p91: CAD file, 2026-01-30]
Data Logger/data logger box with dividers lid.stl
143.5 x 73.2 x 10.0
