3d-paws/3D-PAWS-Print-Files/Light Sensor/board soldering jig.stl

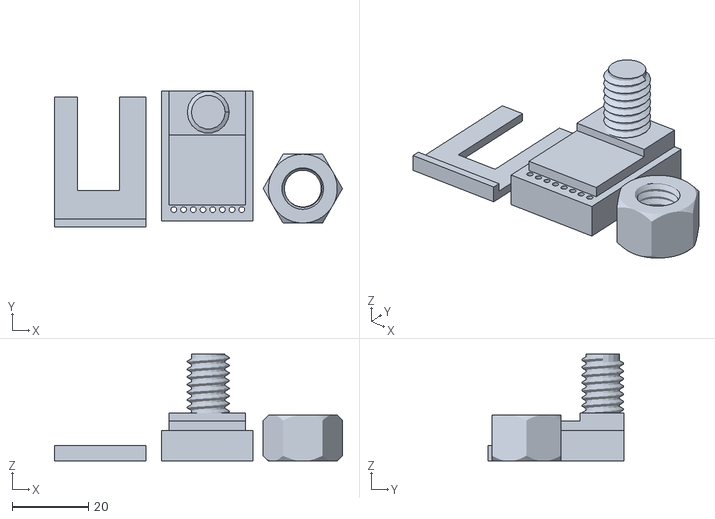
[picture p92: CAD file, 2025-01-09]
Light Sensor/board soldering jig.stl
75.4 x 35.5 x 28.0
