3d-paws/3D-PAWS-Print-Files/Radiation Shield and Wiring/RS Assembly/closed leaf no shaft.stl

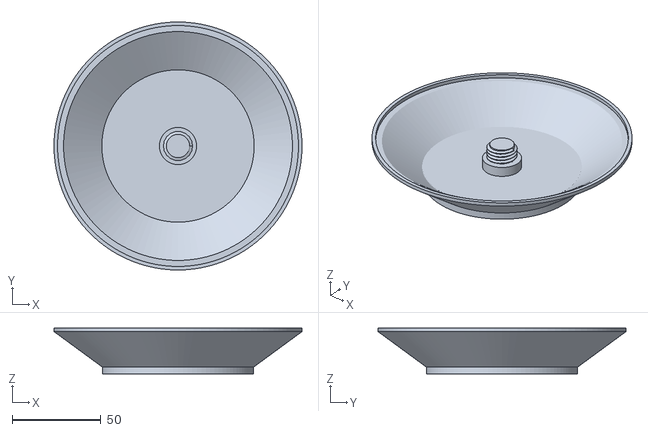
[picture p93: CAD file, 2025-01-09]
Radiation Shield and Wiring/RS Assembly/closed leaf no shaft.stl
140.0 x 140.0 x 25.9
