3d-paws/3D-PAWS-Print-Files/Radiation Shield and Wiring/Wiring/sht breather.stl

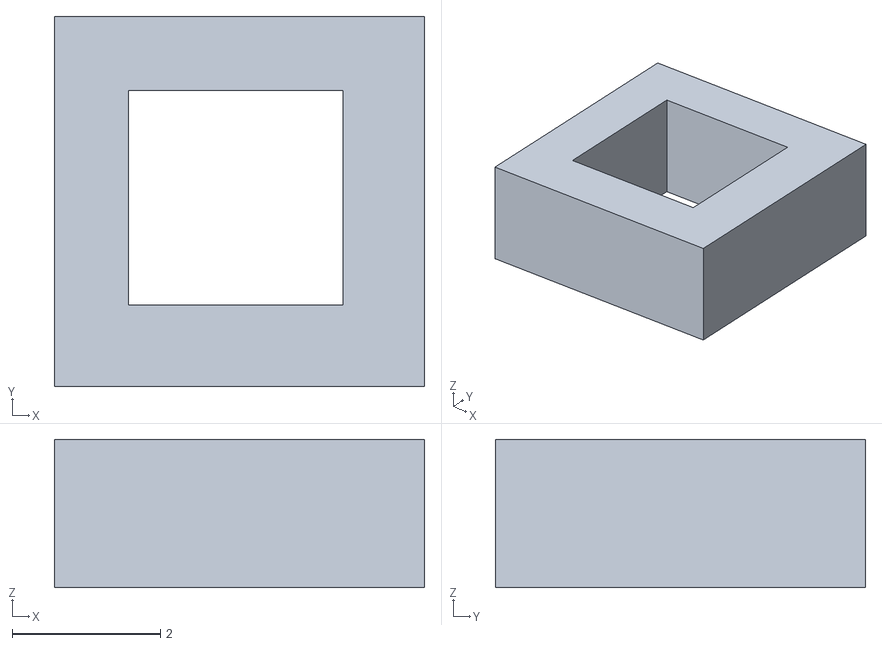
[picture p94: CAD file, 2025-01-09]
Radiation Shield and Wiring/Wiring/sht breather.stl
5.00 x 5.00 x 2.00
