3d-paws/3D-PAWS-Print-Files/Rain Gauge Calibration/inspection cover.stl

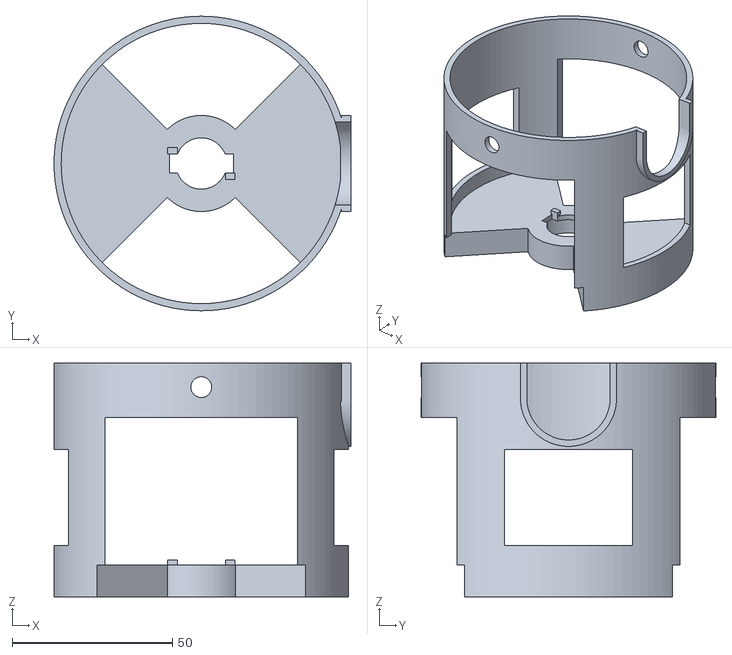
[picture p95: CAD file, 2025-01-10]
Rain Gauge Calibration/inspection cover.stl
92.8 x 92.0 x 73.0
