3d-paws/3D-PAWS-Print-Files/Rain Gauge/5.5 stop.stl

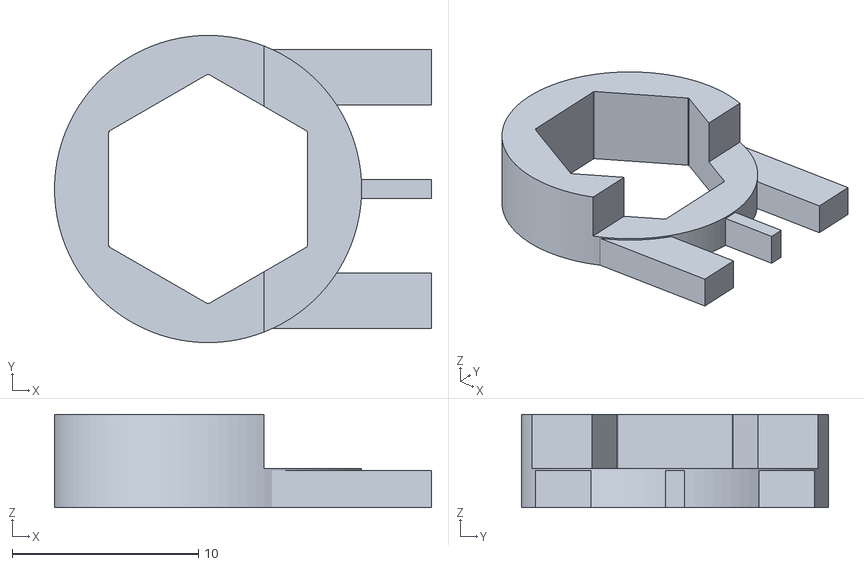
[picture p96: CAD file, 2025-01-10]
Rain Gauge/5.5 stop.stl
20.2 x 16.5 x 5.00
