3d-paws/3D-PAWS-Print-Files/Soil Moisture and Temperature/Installation Tool/actuator.stl

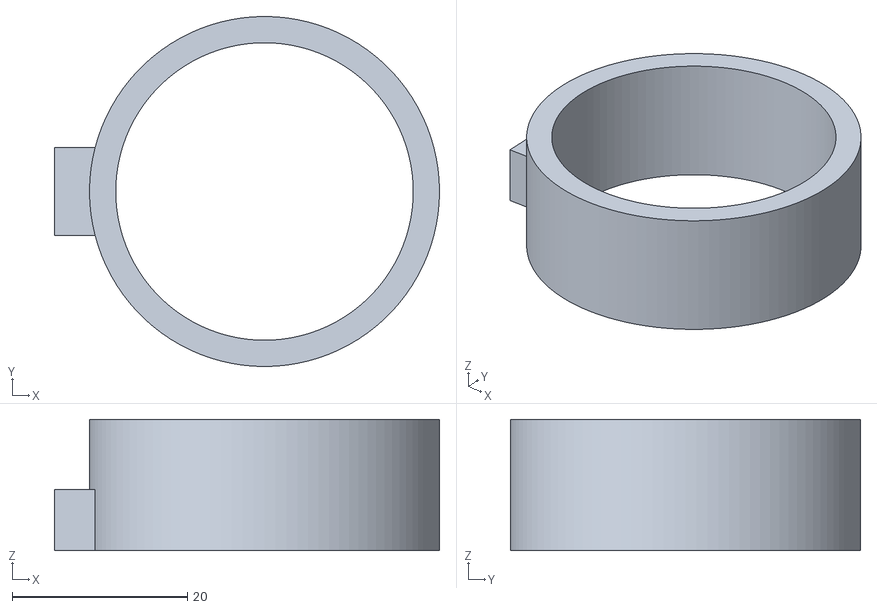
[picture p97: CAD file, 2025-10-24]
Soil Moisture and Temperature/Installation Tool/actuator.stl
44.0 x 40.0 x 15.0
