3d-paws/3D-PAWS-Print-Files/Station Assembly/small M5 connector holder.stl

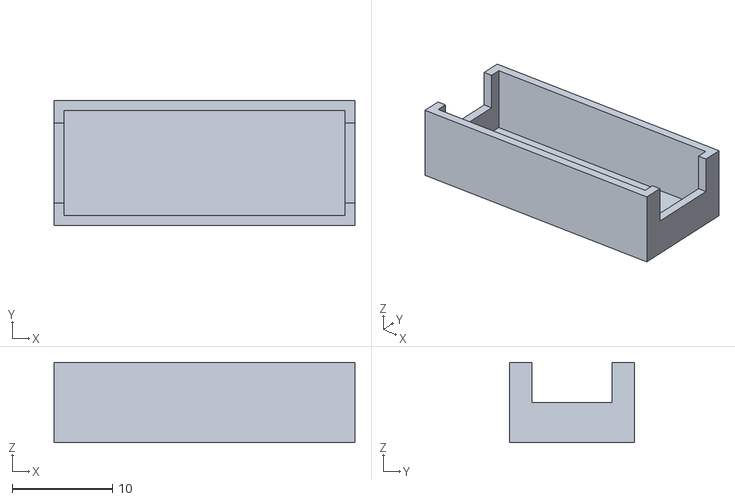
[picture p98: CAD file, 2025-01-10]
Station Assembly/small M5 connector holder.stl
30.0 x 12.5 x 8.00
