3d-paws/3D-PAWS-Print-Files/Stream Gauge/sensor shield.stl

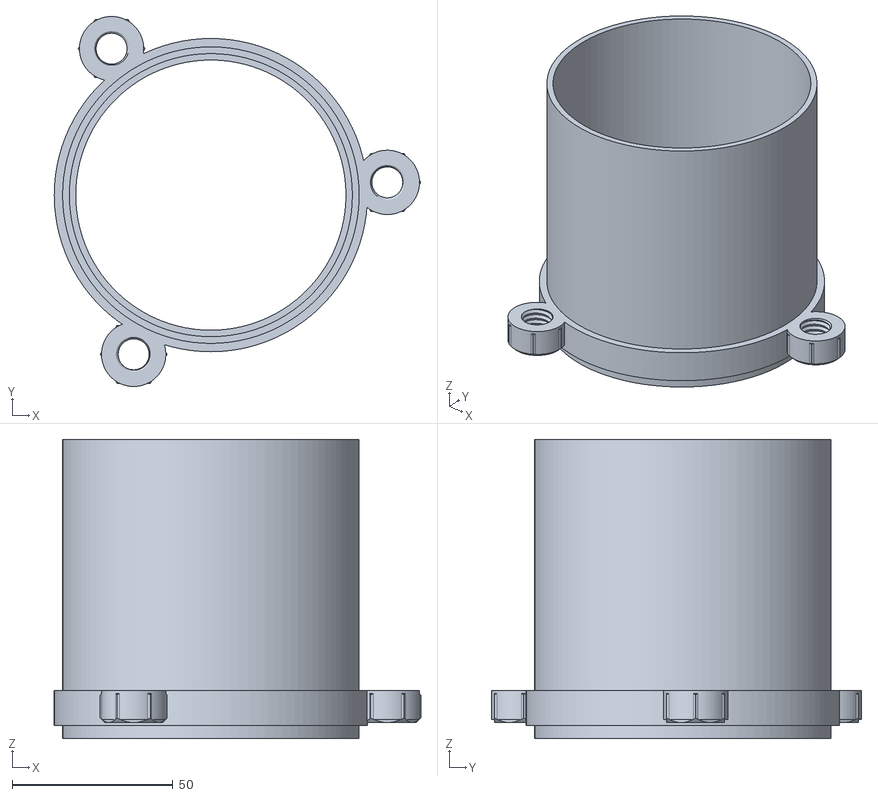
[picture p99: CAD file, 2025-01-10]
Stream Gauge/sensor shield.stl
114.0 x 115.0 x 93.0
