3d-paws/3D-PAWS-Print-Files/Variable Diameter Pipe/32mm/EFTE voltaic clamp LH.stl

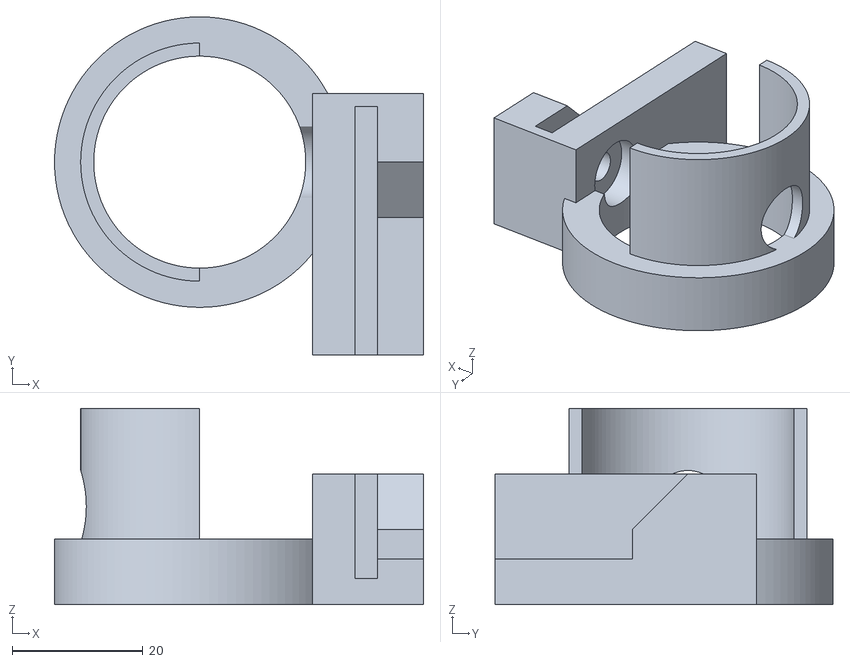
[picture p100: CAD file, 2026-02-09]
Variable Diameter Pipe/32mm/EFTE voltaic clamp LH.stl
56.4 x 51.7 x 30.0
