3d-paws/3D-PAWS-Print-Files/Wind Vane/pointer.stl

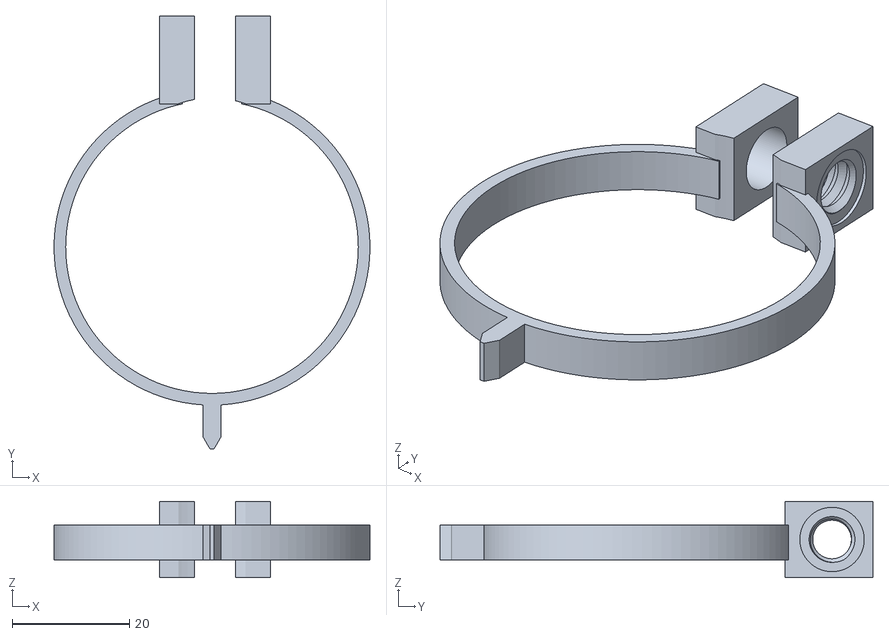
[picture p101: CAD file, 2025-01-09]
Wind Vane/pointer.stl
54.0 x 74.0 x 13.0
