3d-paws/3D-PAWS-Print-Files/Air Quality/AQ center screen.stl

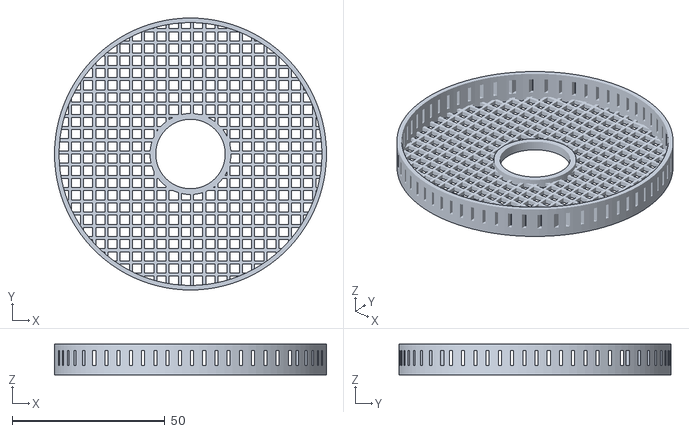
[picture p102: CAD file, 2026-02-04]
Air Quality/AQ center screen.stl
89.0 x 89.0 x 10.0
