3d-paws/3D-PAWS-Print-Files/Anemometer/cup.stl

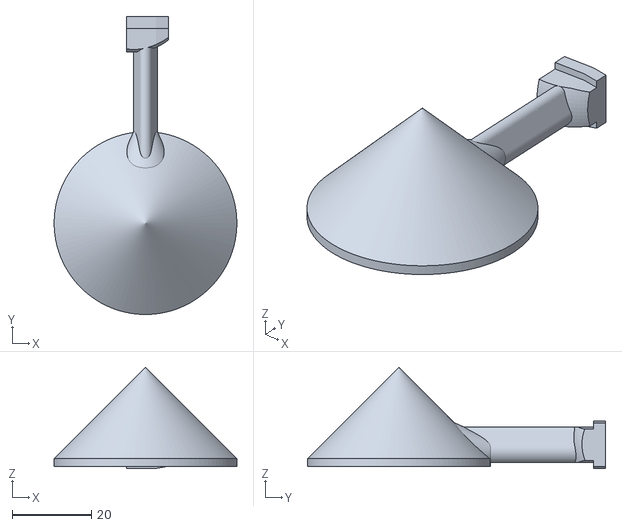
[picture p103: CAD file, 2025-01-09]
Anemometer/cup.stl
46.0 x 75.0 x 25.5
