3d-paws/3D-PAWS-Print-Files/Data Logger/data logger box with dividers.stl

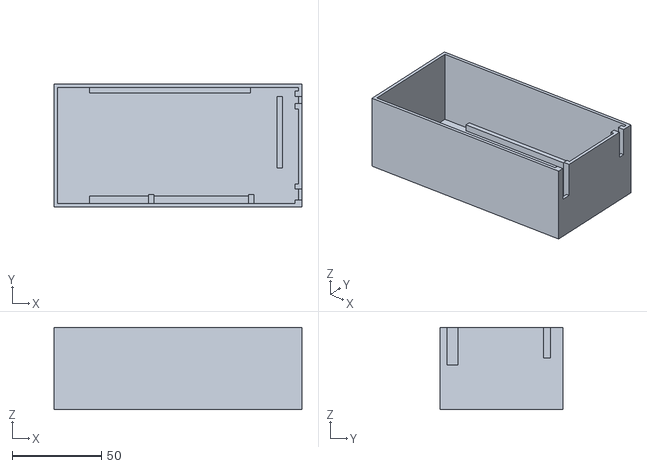
[picture p104: CAD file, 2026-01-30]
Data Logger/data logger box with dividers.stl
139.0 x 69.0 x 46.0
