3d-paws/3D-PAWS-Print-Files/Radiation Shield and Wiring/RS Assembly/center screen vented wall.stl

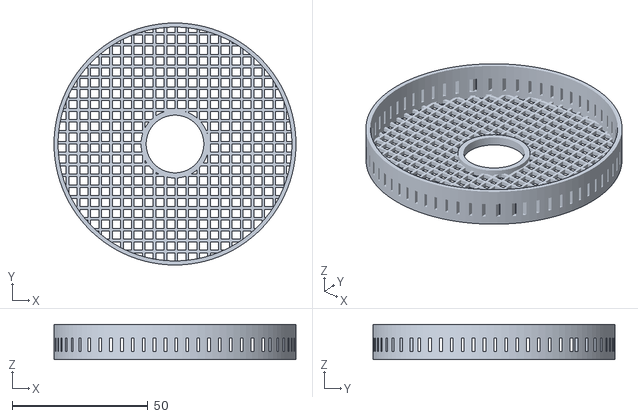
[picture p105: CAD file, 2025-01-09]
Radiation Shield and Wiring/RS Assembly/center screen vented wall.stl
89.0 x 89.0 x 13.0
