3d-paws/3D-PAWS-Print-Files/Rain Gauge Calibration/pumped drip controller.stl

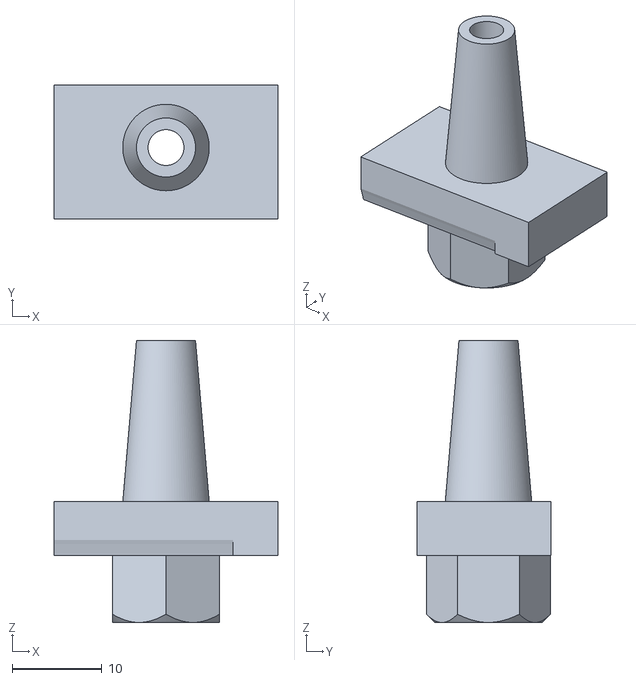
[picture p106: CAD file, 2025-01-10]
Rain Gauge Calibration/pumped drip controller.stl
25.0 x 15.0 x 31.5
