3d-paws/3D-PAWS-Print-Files/Rain Gauge/sensor holder.stl

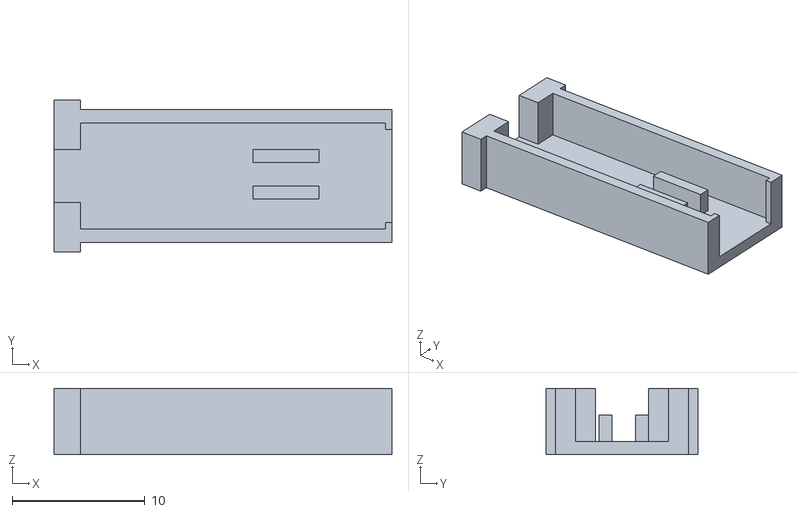
[picture p107: CAD file, 2025-01-10]
Rain Gauge/sensor holder.stl
25.5 x 11.5 x 5.00
