3d-paws/3D-PAWS-Print-Files/Snow Gauge/top leaf snow.stl

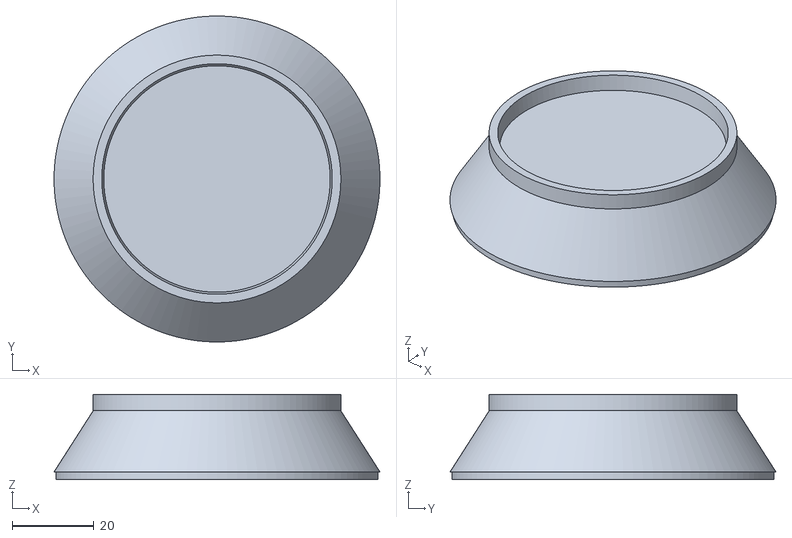
[picture p108: CAD file, 2025-01-10]
Snow Gauge/top leaf snow.stl
80.0 x 80.0 x 20.9
