3d-paws/3D-PAWS-Print-Files/Soil Moisture and Temperature/Installation Tool/lower pivot.stl

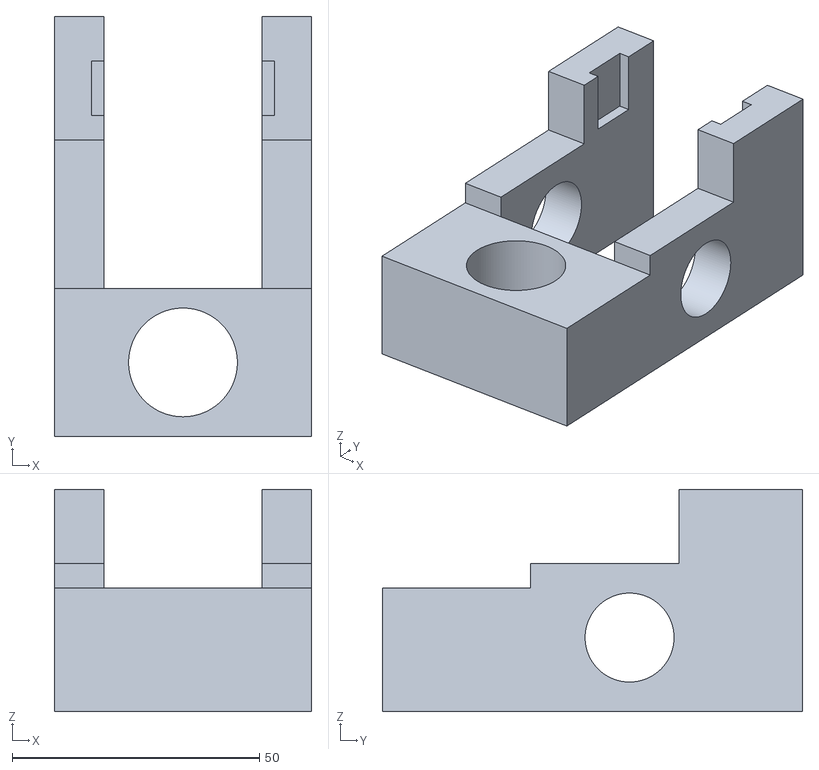
[picture p109: CAD file, 2025-10-24]
Soil Moisture and Temperature/Installation Tool/lower pivot.stl
52.0 x 85.0 x 45.0
