3d-paws/3D-PAWS-Print-Files/Stream Gauge/swivel.stl

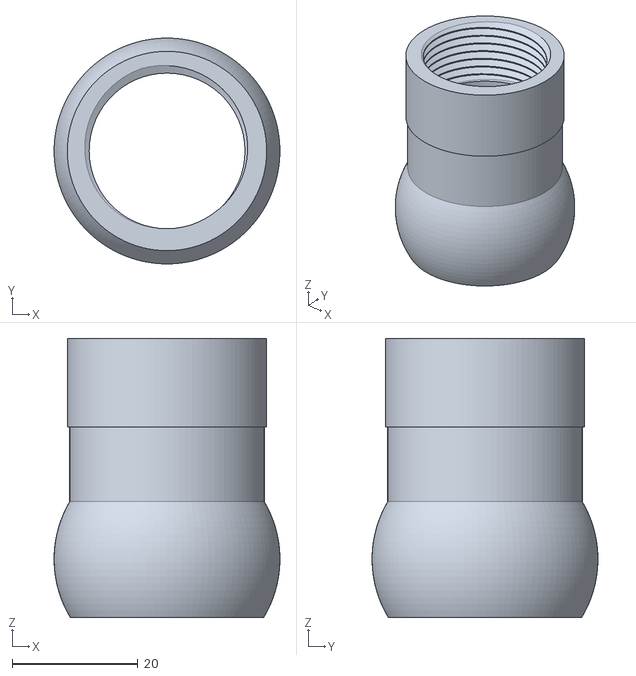
[picture p110: CAD file, 2025-01-10]
Stream Gauge/swivel.stl
36.0 x 36.0 x 44.4
