3d-paws/3D-PAWS-Print-Files/Tools/multi tool.stl

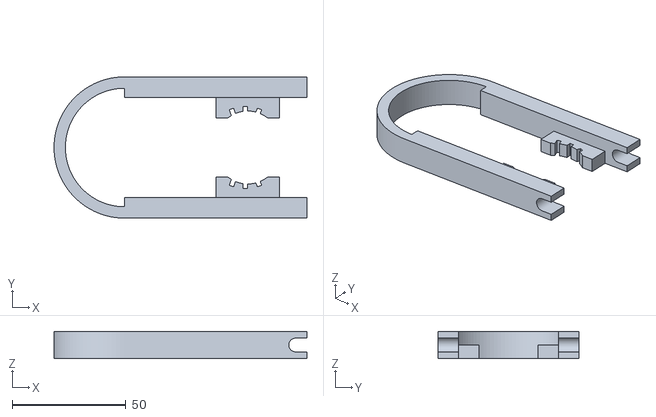
[picture p111: CAD file, 2026-02-25]
Tools/multi tool.stl
111.0 x 62.0 x 12.0
