3d-paws/3D-PAWS-Print-Files/Variable Diameter Pipe/32mm/EFTE voltaic clamp.stl

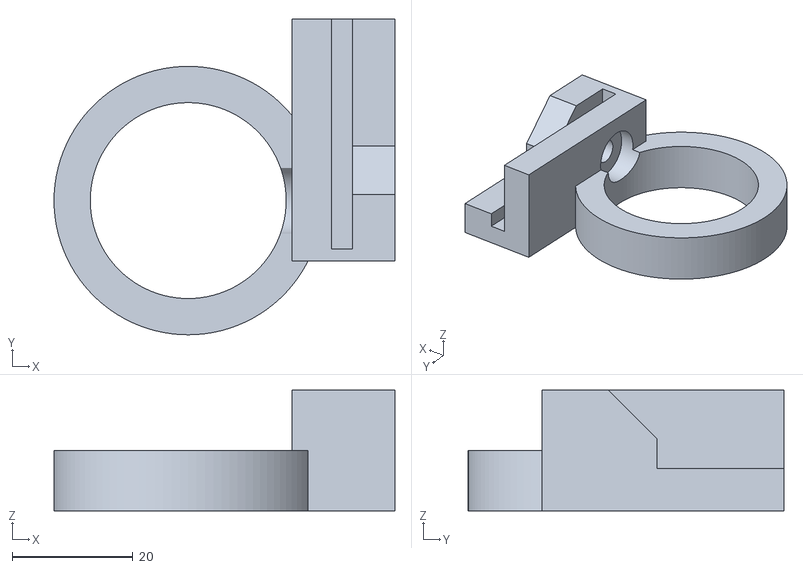
[picture p112: CAD file, 2026-02-09]
Variable Diameter Pipe/32mm/EFTE voltaic clamp.stl
56.4 x 52.2 x 20.0
