3d-paws/3D-PAWS-Print-Files/Wind Vane/rotor.stl

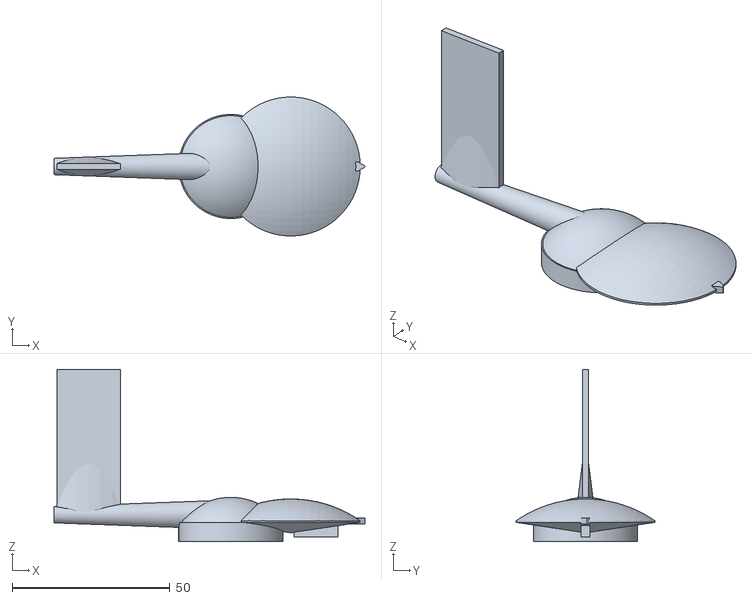
[picture p113: CAD file, 2025-01-09]
Wind Vane/rotor.stl
98.5 x 44.0 x 54.5
