3d-paws/3D-PAWS-Print-Files/Air Quality/air quality sensor seat.stl

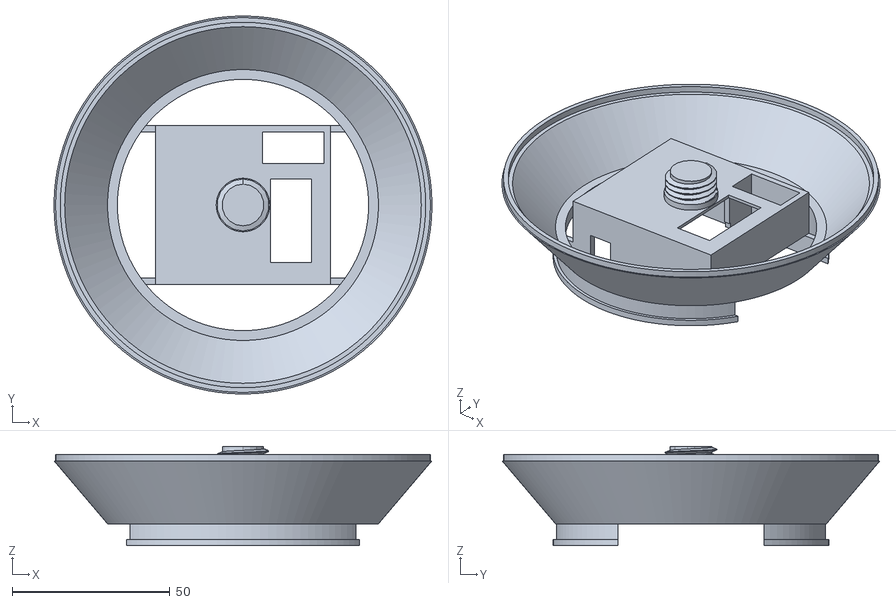
[picture p114: CAD file, 2026-02-04]
Air Quality/air quality sensor seat.stl
120.0 x 120.0 x 31.5
