3d-paws/3D-PAWS-Print-Files/Data Logger/antenna clip argon.stl

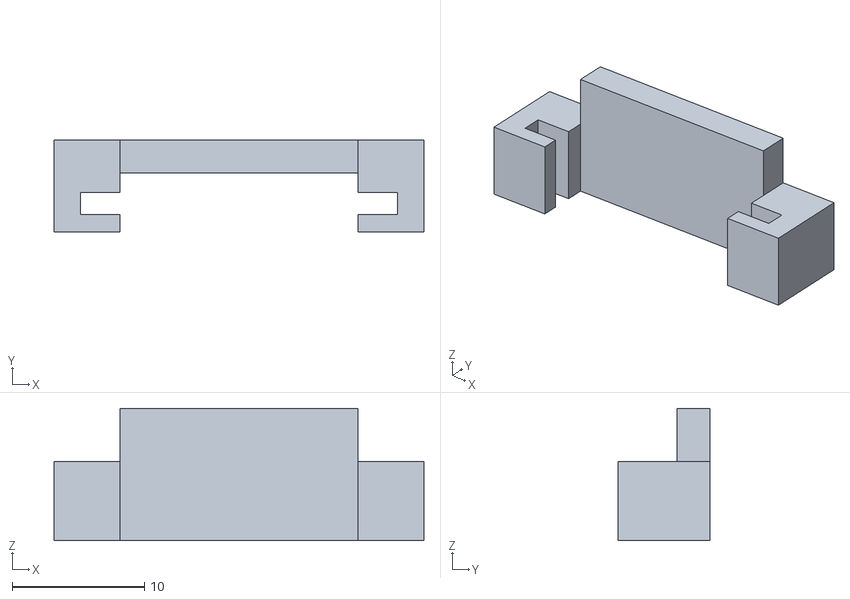
[picture p115: CAD file, 2025-01-10]
Data Logger/antenna clip argon.stl
28.0 x 7.00 x 10.0
