3d-paws/3D-PAWS-Print-Files/Radiation Shield and Wiring/RS Assembly/base cover.stl

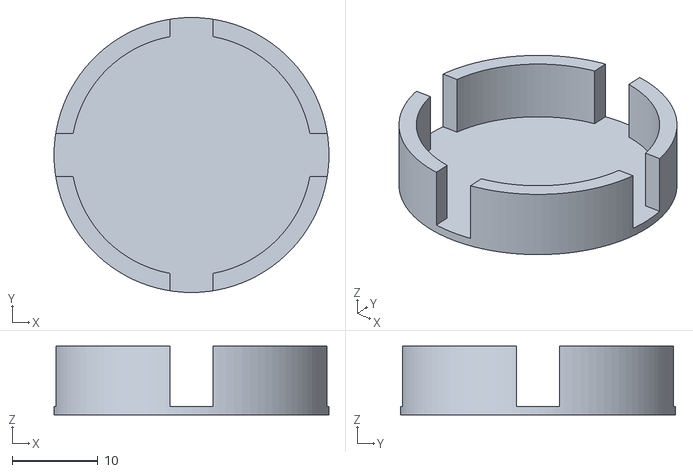
[picture p116: CAD file, 2025-01-09]
Radiation Shield and Wiring/RS Assembly/base cover.stl
32.0 x 32.0 x 8.00
