3d-paws/3D-PAWS-Print-Files/Rain Gauge Calibration/universal clamp for 1 in pipe.stl

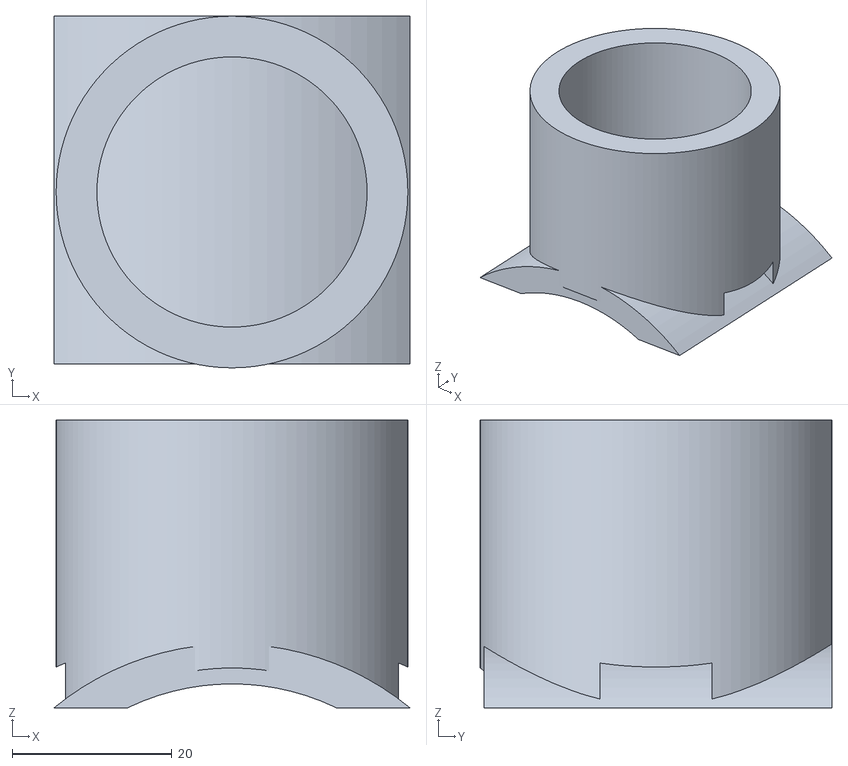
[picture p117: CAD file, 2025-01-10]
Rain Gauge Calibration/universal clamp for 1 in pipe.stl
44.5 x 44.0 x 36.0
