3d-paws/3D-PAWS-Print-Files/Rain Gauge/4.5 stop.stl

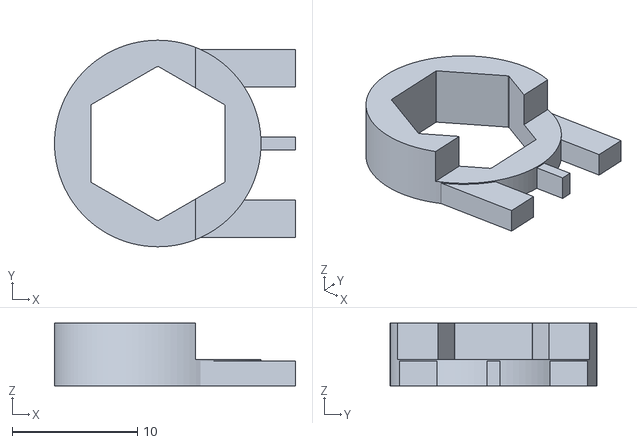
[picture p118: CAD file, 2025-01-10]
Rain Gauge/4.5 stop.stl
19.2 x 16.5 x 5.00
