3d-paws/3D-PAWS-Print-Files/Snow Gauge/blanking plug.stl

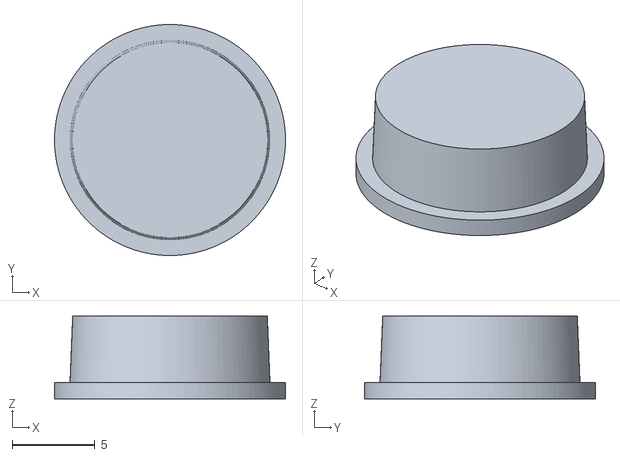
[picture p119: CAD file, 2025-01-10]
Snow Gauge/blanking plug.stl
14.0 x 14.0 x 5.00
