3d-paws/3D-PAWS-Print-Files/Tools/direction setter.stl

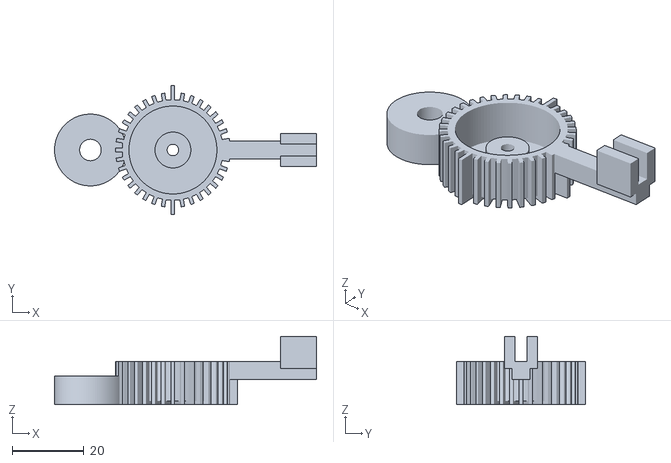
[picture p120: CAD file, 2026-02-25]
Tools/direction setter.stl
73.0 x 36.0 x 19.0
