3d-paws/3D-PAWS-Print-Files/Variable Diameter Pipe/32mm/universal clamp for 1 in pipe.stl

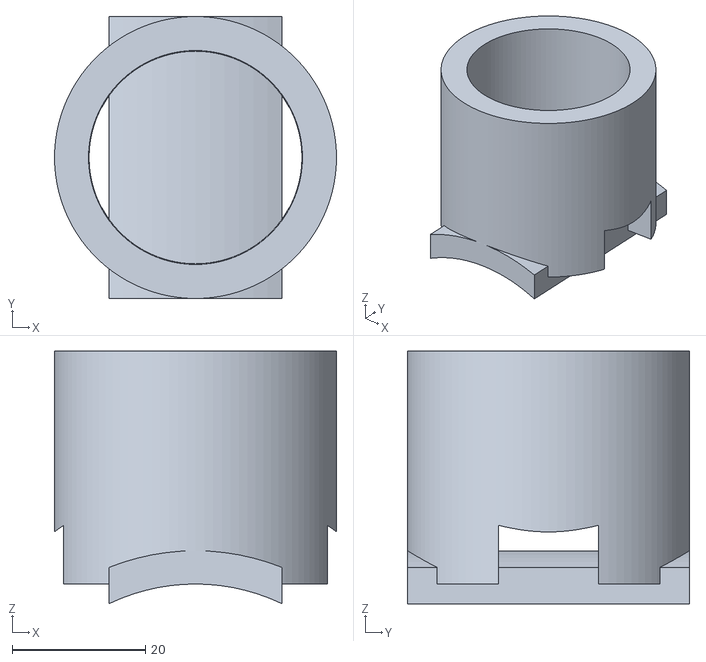
[picture p121: CAD file, 2026-02-09]
Variable Diameter Pipe/32mm/universal clamp for 1 in pipe.stl
42.4 x 42.4 x 38.0
