3d-paws/3D-PAWS-Print-Files/Wind Vane/alignment cap.stl

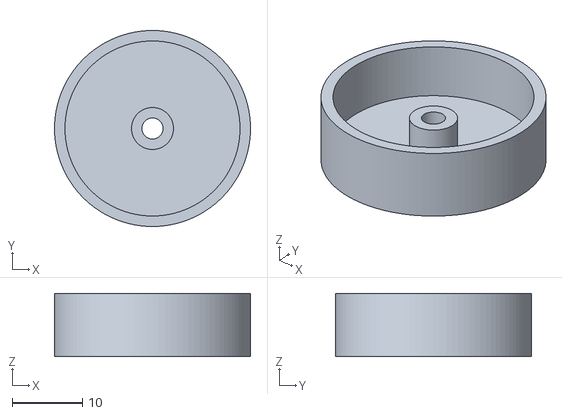
[picture p122: CAD file, 2025-01-09]
Wind Vane/alignment cap.stl
28.0 x 28.0 x 9.00
