3d-paws/3D-PAWS-Print-Files/Air Quality/air quality sensor.3mf

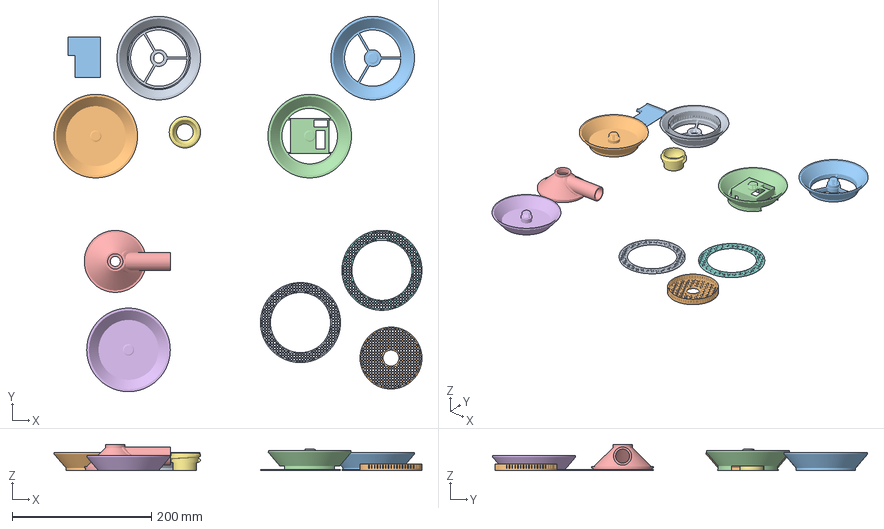
[picture p123: CAD file, 2026-02-04]
Air Quality/air quality sensor.3mf
528.4 x 539.0 x 38.0 mm
air quality 2nd leaf.stl
air quality closed leaf.stl
air quality open leaf.stl
air quality sensor seat.stl
conical base no shaft.stl
air quality top leaf.stl
locking threads.stl
AQ screen ring.stl x 2
AQ center screen.stl
air quality sensor cover.stl
