3d-paws/3D-PAWS-Print-Files/Anemometer/body.stl

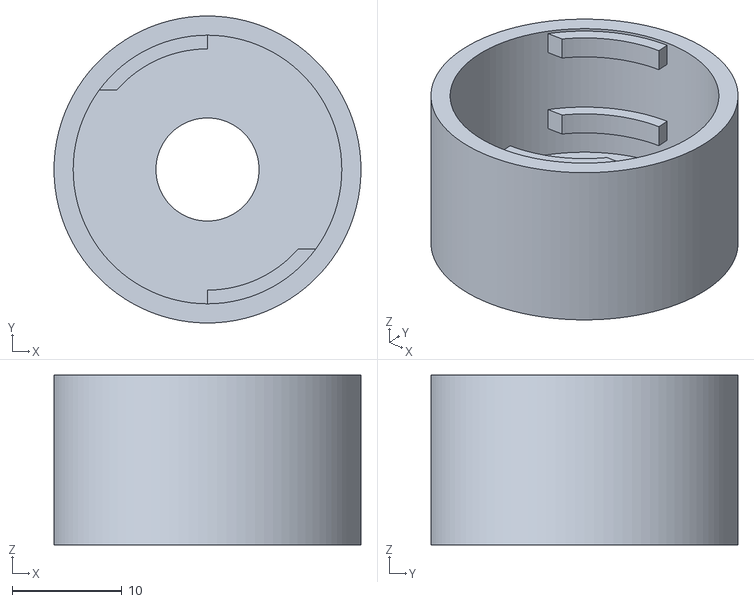
[picture p124: CAD file, 2025-01-09]
Anemometer/body.stl
28.0 x 28.0 x 15.5
