3d-paws/3D-PAWS-Print-Files/Rain Gauge/bucket retainer.stl

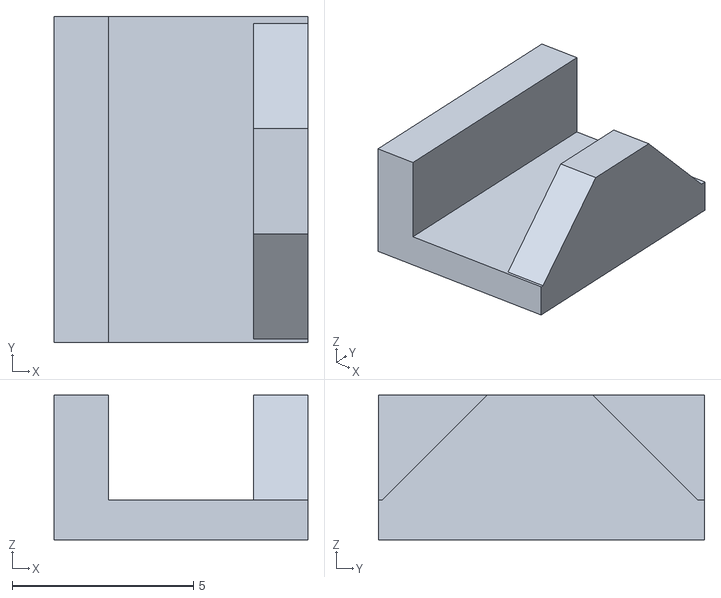
[picture p126: CAD file, 2025-01-10]
Rain Gauge/bucket retainer.stl
7.00 x 9.00 x 4.00
