3d-paws/3D-PAWS-Print-Files/Snow Gauge/snow cone cover.stl

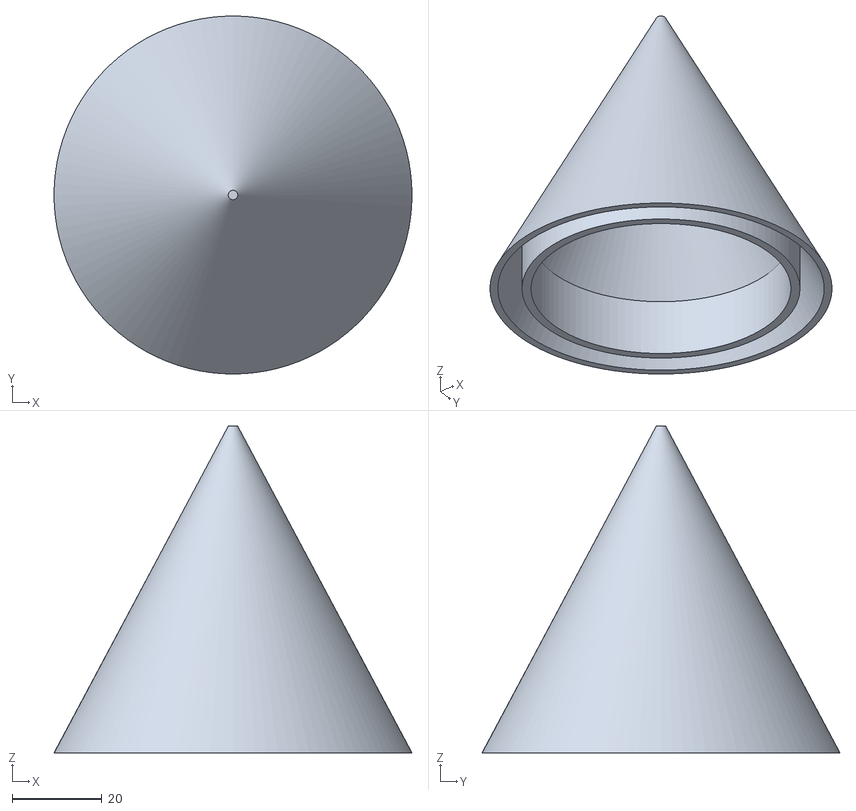
[picture p127: CAD file, 2025-01-10]
Snow Gauge/snow cone cover.stl
80.0 x 80.0 x 73.0
