3d-paws/3D-PAWS-Print-Files/Station Assembly/box adapter male.stl

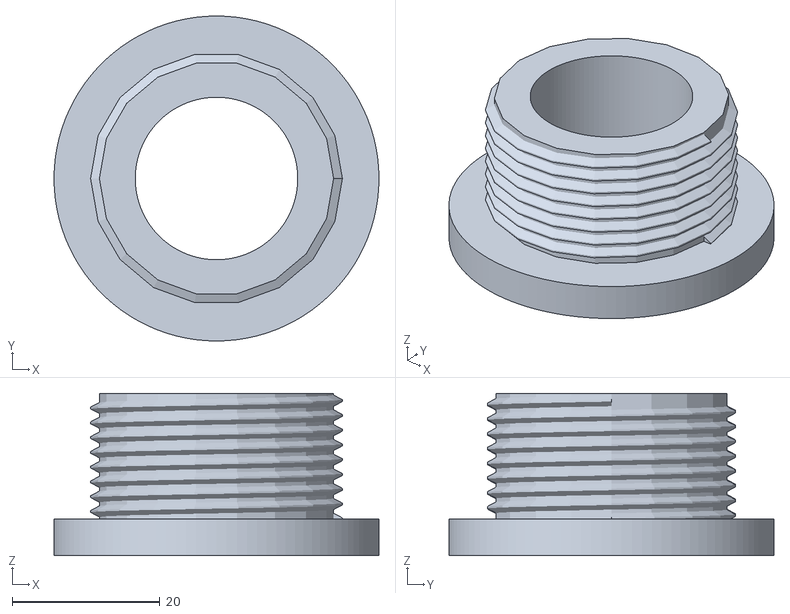
[picture p128: CAD file, 2025-01-10]
Station Assembly/box adapter male.stl
44.0 x 44.0 x 22.0
