3d-paws/3D-PAWS-Print-Files/Tools/loom.stl

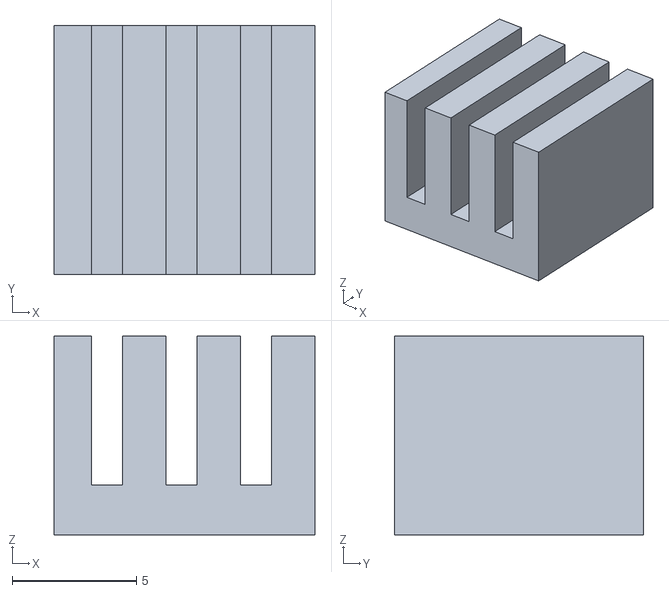
[picture p129: CAD file, 2026-02-25]
Tools/loom.stl
10.5 x 10.0 x 8.00
