3d-paws/3D-PAWS-Print-Files/Variable Diameter Pipe/32mm/wind mount.stl

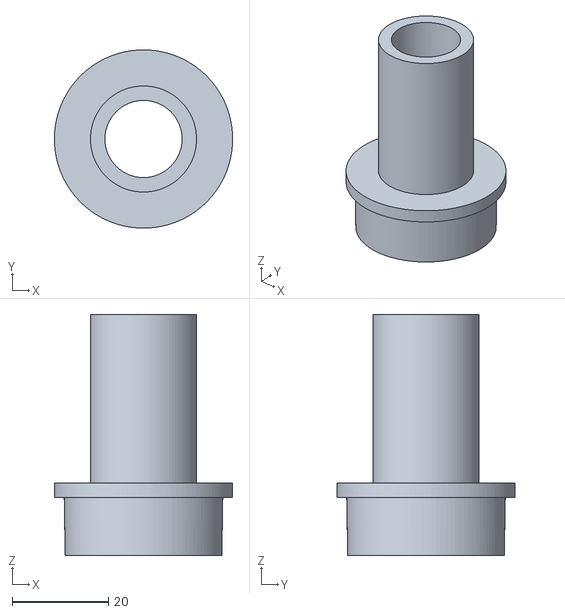
[picture p130: CAD file, 2026-02-09]
Variable Diameter Pipe/32mm/wind mount.stl
37.0 x 37.0 x 50.0
