3d-paws/3D-PAWS-Print-Files/Wind Vane/flat cover.stl

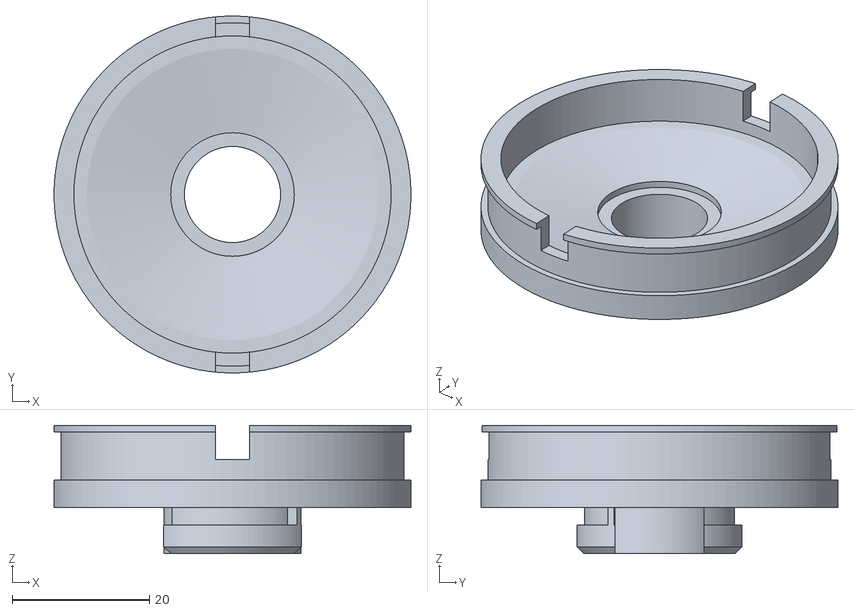
[picture p131: CAD file, 2025-01-09]
Wind Vane/flat cover.stl
52.0 x 52.0 x 18.7
