3d-paws/3D-PAWS-Print-Files/Air Quality/air quality top leaf.stl

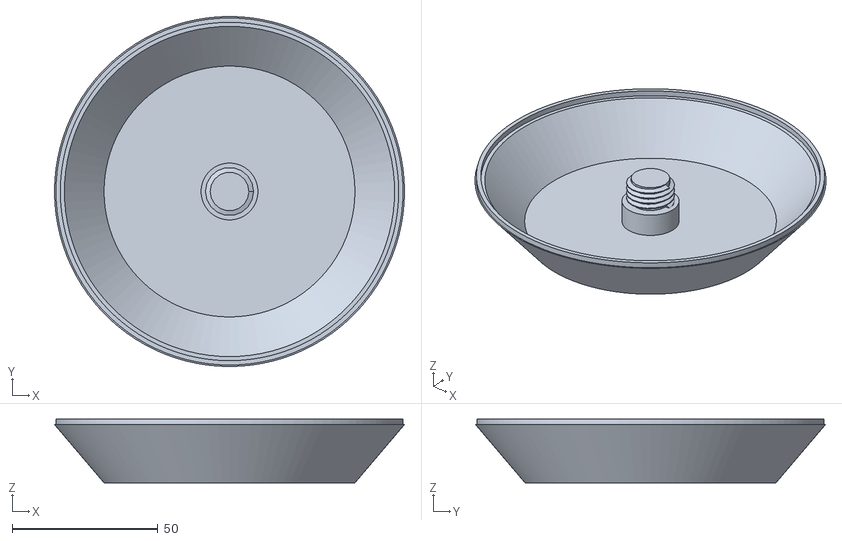
[picture p132: CAD file, 2026-02-04]
Air Quality/air quality top leaf.stl
120.0 x 120.0 x 21.9
