3d-paws/3D-PAWS-Print-Files/Rain Gauge/fastner.stl

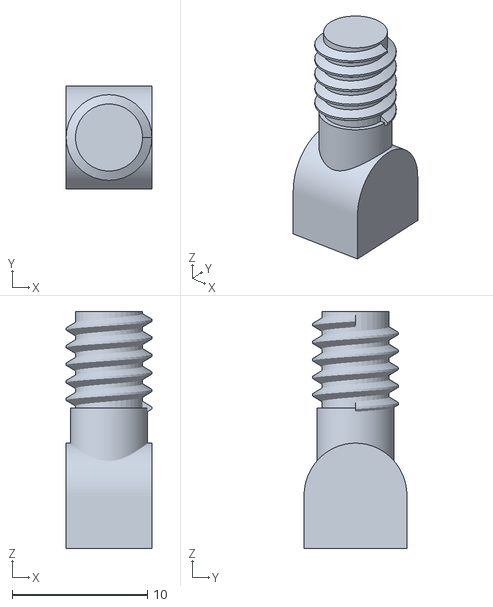
[picture p133: CAD file, 2025-01-10]
Rain Gauge/fastner.stl
6.35 x 7.62 x 17.5
