3d-paws/3D-PAWS-Print-Files/Snow Gauge/Snow gauge rad shield base.stl

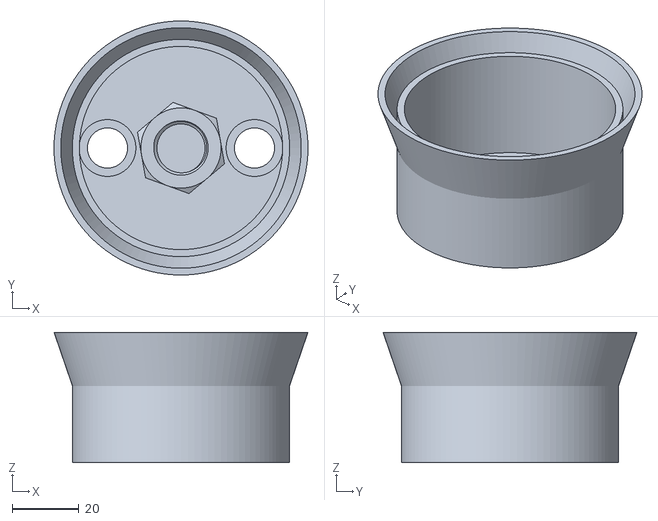
[picture p134: CAD file, 2025-01-10]
Snow Gauge/Snow gauge rad shield base.stl
76.0 x 76.0 x 39.0
