3d-paws/3D-PAWS-Print-Files/Station Assembly/levelling joint olive.stl

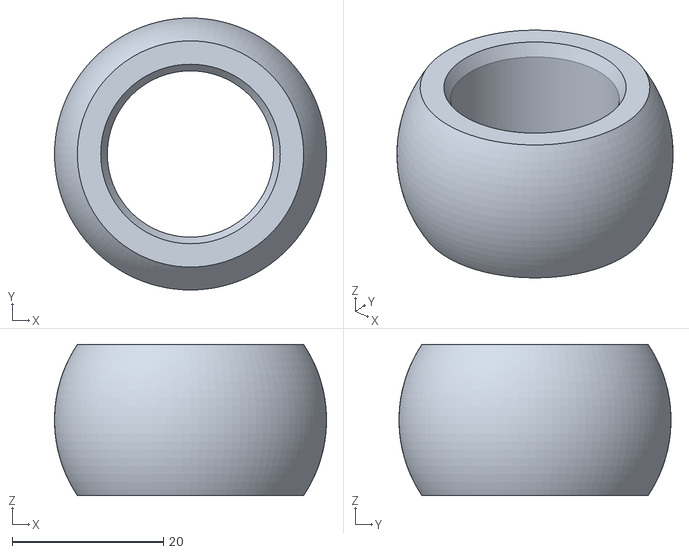
[picture p135: CAD file, 2025-01-10]
Station Assembly/levelling joint olive.stl
36.0 x 36.0 x 20.0
