3d-paws/3D-PAWS-Print-Files/Tools/wind levelling tool.stl

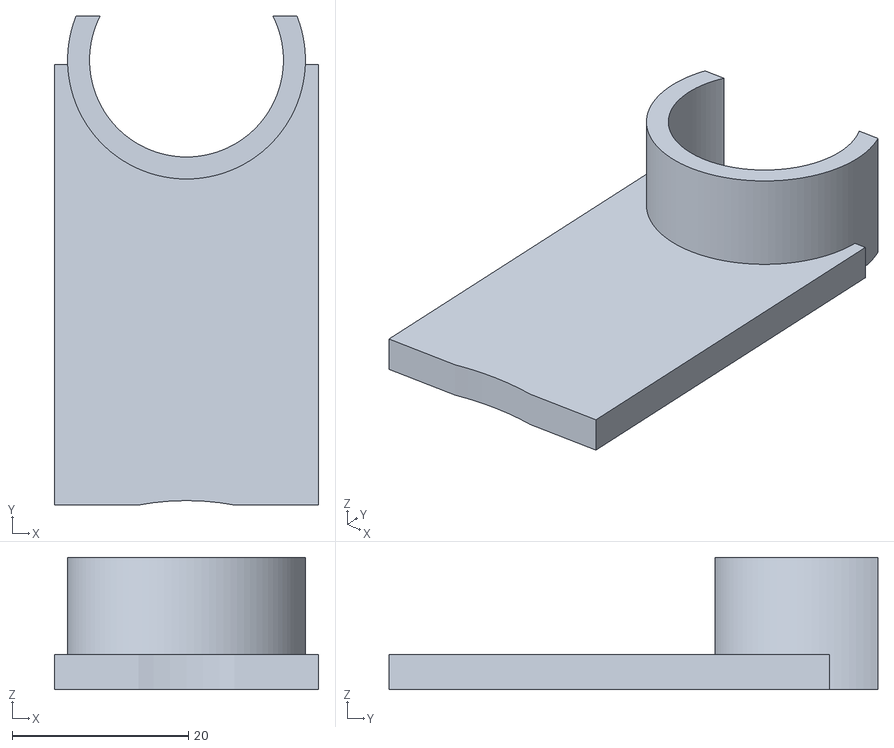
[picture p136: CAD file, 2026-01-30]
Tools/wind levelling tool.stl
30.0 x 55.5 x 15.0
