3d-paws/3D-PAWS-Print-Files/Variable Diameter Pipe/32mm/RG upper cover clamp.stl

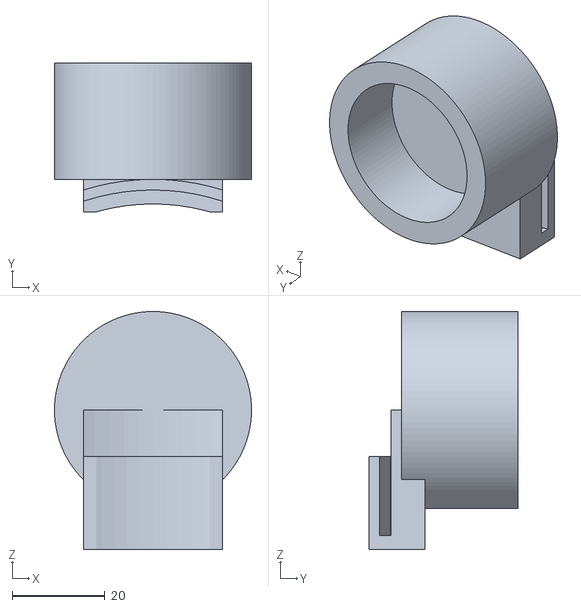
[picture p137: CAD file, 2026-02-09]
Variable Diameter Pipe/32mm/RG upper cover clamp.stl
42.4 x 32.0 x 51.2
