3d-paws/3D-PAWS-Print-Files/Rain Gauge/bucket.stl

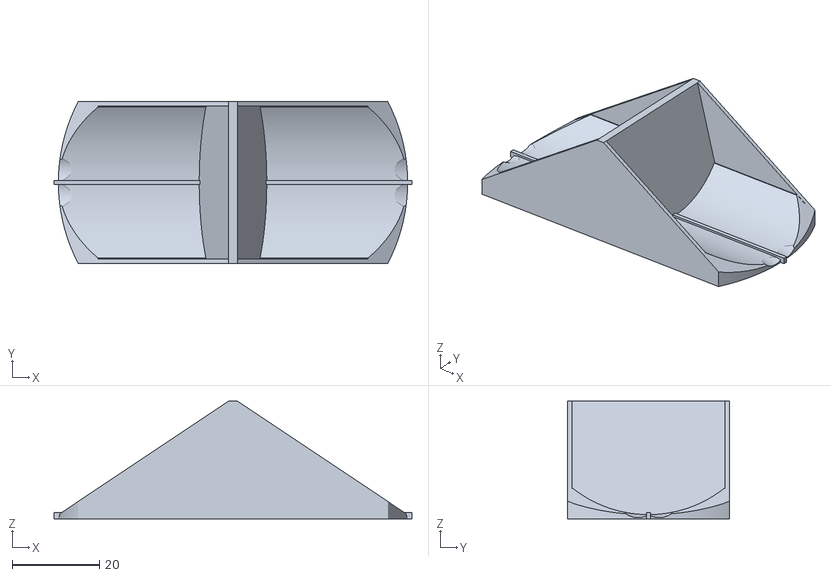
[picture p138: CAD file, 2025-01-10]
Rain Gauge/bucket.stl
82.0 x 37.0 x 27.0
